buk7456/FreeTX/doc/images/img1.png

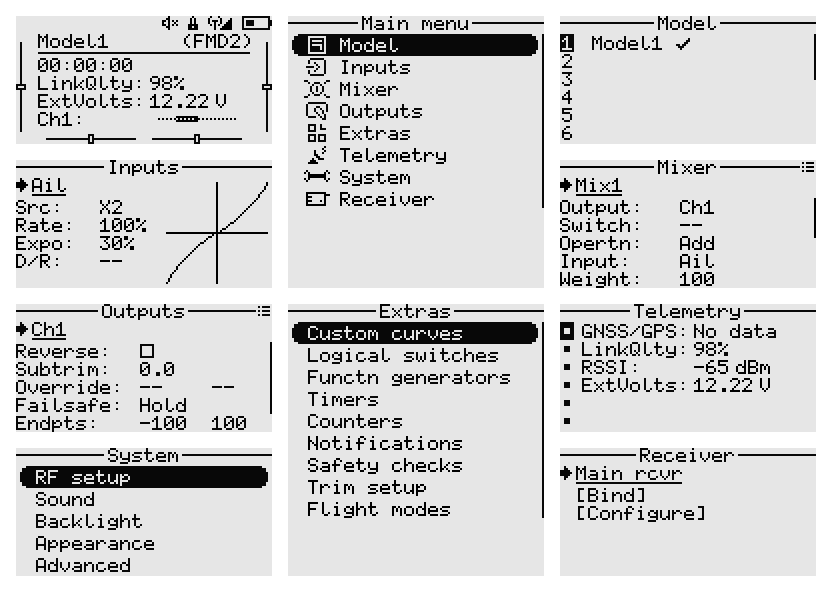
doc/images/img1.png
