buk7456/FreeTX/doc/images/img3.jpg

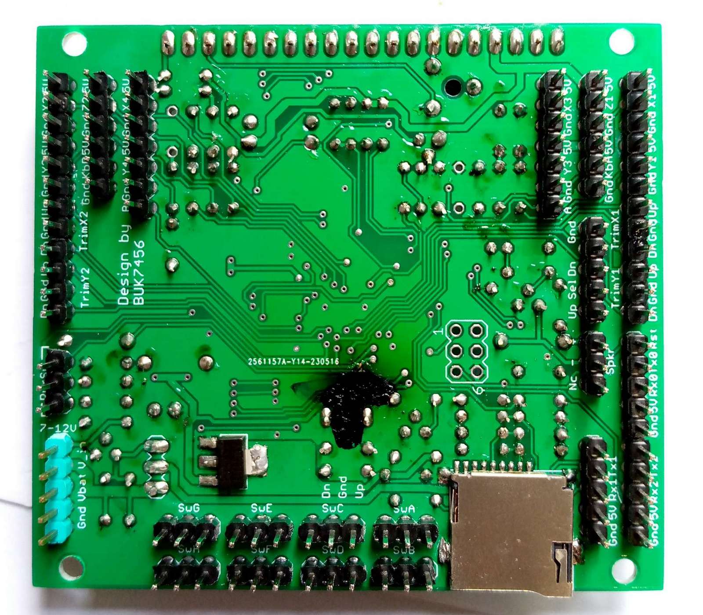
doc/images/img3.jpg
