buk7456/FreeTX/doc/images/img7.jpg

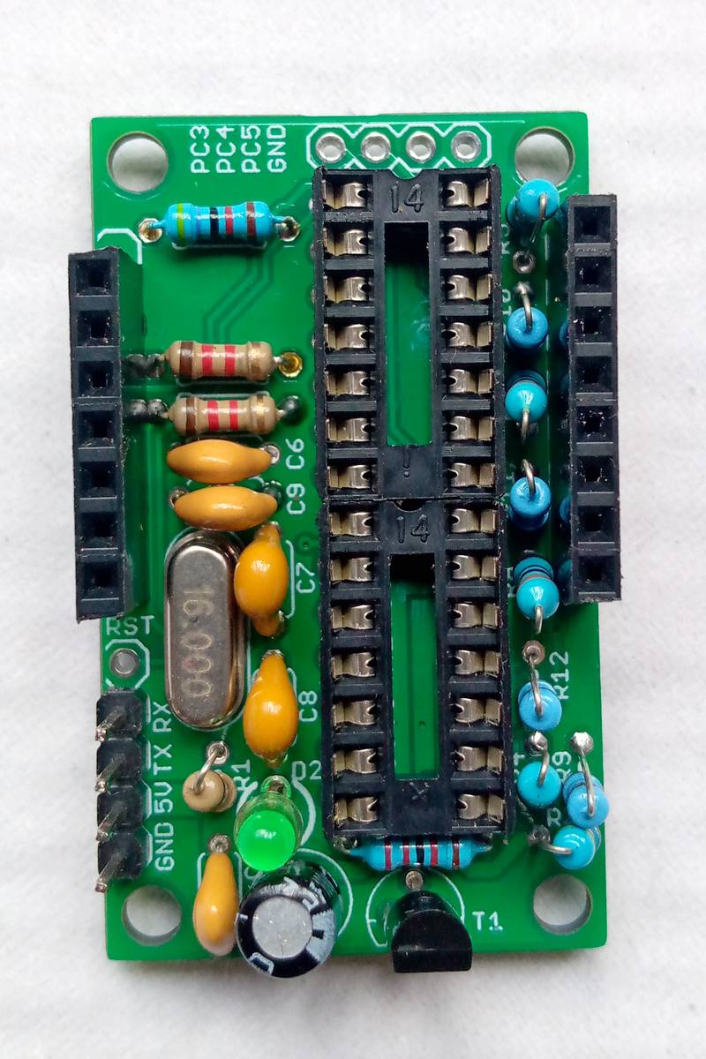
doc/images/img7.jpg
