buk7456/FreeTX/doc/images/img8.jpg

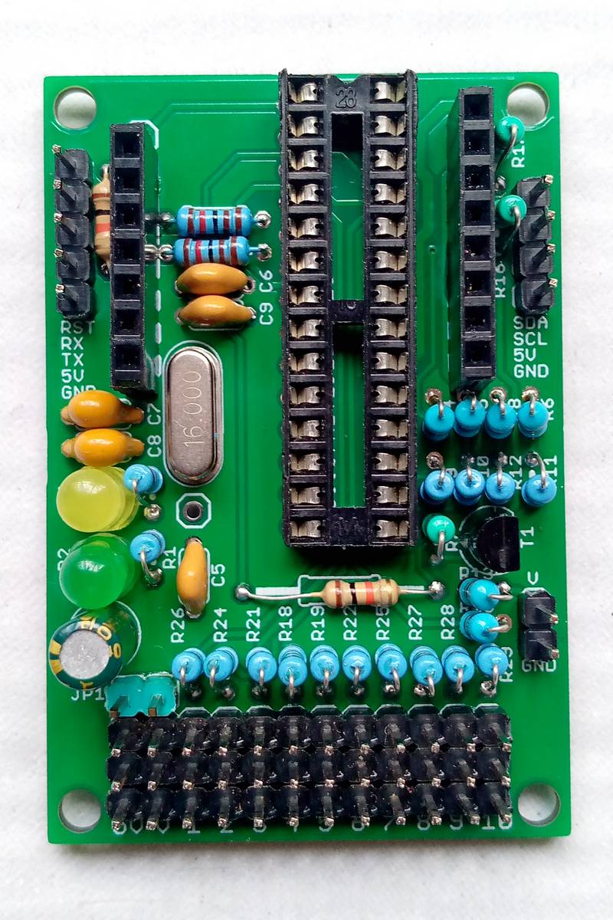
doc/images/img8.jpg
