buk7456/FreeTX/doc/images/img9.jpg

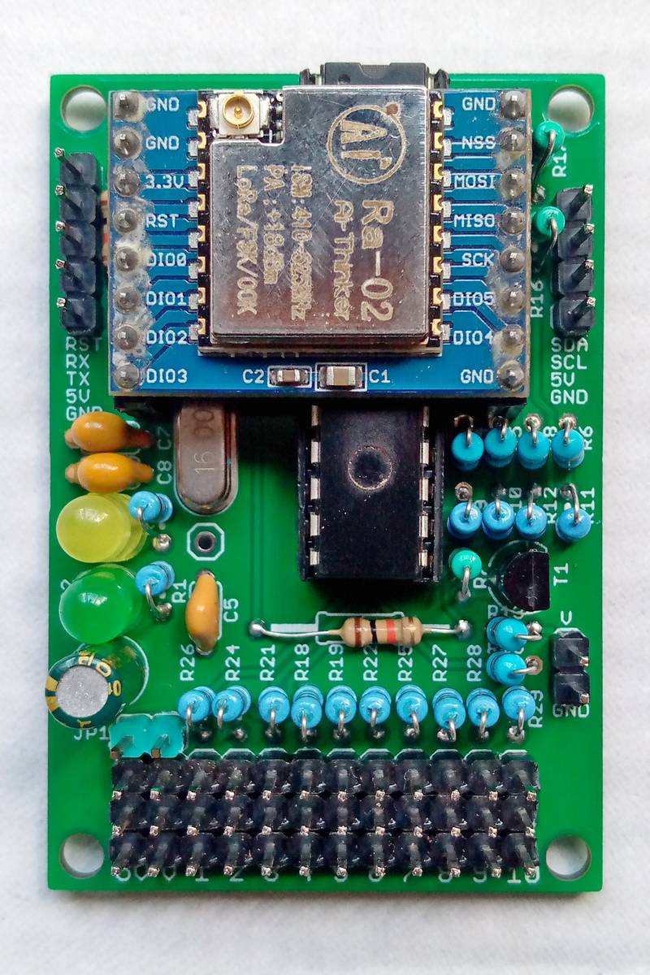
doc/images/img9.jpg
