buk7456/FreeTX/doc/images/screenshots/counters_context_menu.png

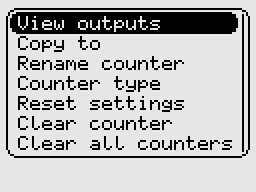
doc/images/screenshots/counters_context_menu.png
