buk7456/FreeTX/doc/images/screenshots/curve_landing_gear_sequencer_1.png

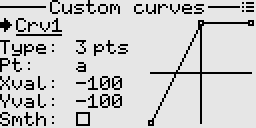
doc/images/screenshots/curve_landing_gear_sequencer_1.png
