buk7456/FreeTX/doc/images/screenshots/curves_landing_gear_sequencer_advanced_v1_1.png

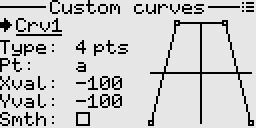
doc/images/screenshots/curves_landing_gear_sequencer_advanced_v1_1.png
