buk7456/FreeTX/doc/images/screenshots/curves_landing_gear_sequencer_advanced_v2_2.png

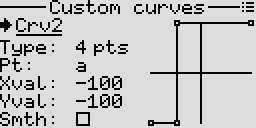
doc/images/screenshots/curves_landing_gear_sequencer_advanced_v2_2.png
