buk7456/FreeTX/doc/images/screenshots/custom_curves_context_menu.png

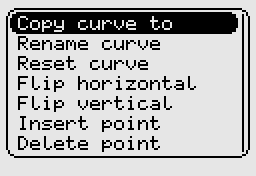
doc/images/screenshots/custom_curves_context_menu.png
