buk7456/FreeTX/doc/images/screenshots/function_generators_context_menu.png

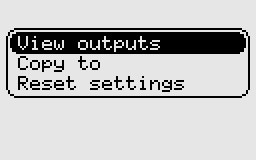
doc/images/screenshots/function_generators_context_menu.png
