buk7456/FreeTX/doc/images/screenshots/home_screen_context_menu.png

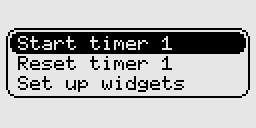
doc/images/screenshots/home_screen_context_menu.png
