buk7456/FreeTX/doc/images/screenshots/inputs_1.png

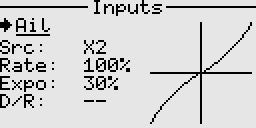
doc/images/screenshots/inputs_1.png
