buk7456/FreeTX/doc/images/screenshots/inputs_2.png

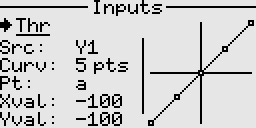
doc/images/screenshots/inputs_2.png
