buk7456/FreeTX/doc/images/screenshots/inputs_3.png

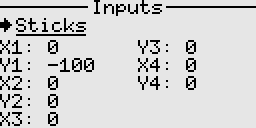
doc/images/screenshots/inputs_3.png
