buk7456/FreeTX/doc/images/screenshots/inputs_4.png

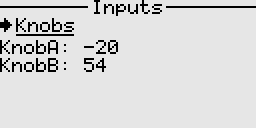
doc/images/screenshots/inputs_4.png
