buk7456/FreeTX/doc/images/screenshots/inputs_5.png

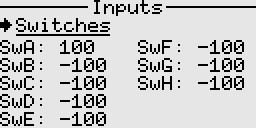
doc/images/screenshots/inputs_5.png
