buk7456/FreeTX/doc/images/screenshots/logical_switches_context_menu.png

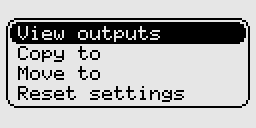
doc/images/screenshots/logical_switches_context_menu.png
