buk7456/FreeTX/doc/images/screenshots/mixer_monitor.png

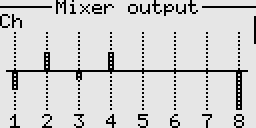
doc/images/screenshots/mixer_monitor.png
