buk7456/FreeTX/doc/images/screenshots/mixer_monitor_with_tooltip.png

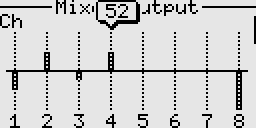
doc/images/screenshots/mixer_monitor_with_tooltip.png
