buk7456/FreeTX/doc/images/screenshots/model_manager_context_menu_free.png

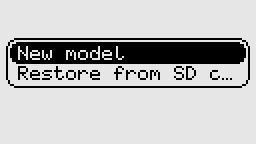
doc/images/screenshots/model_manager_context_menu_free.png
