buk7456/FreeTX/doc/images/screenshots/model_manager_model_type.png

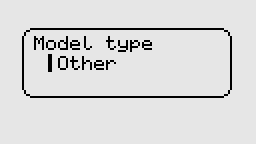
doc/images/screenshots/model_manager_model_type.png
