buk7456/FreeTX/doc/images/screenshots/notifications_context_menu.png

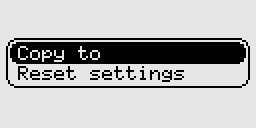
doc/images/screenshots/notifications_context_menu.png
