buk7456/FreeTX/doc/images/screenshots/outputs_context_menu.png

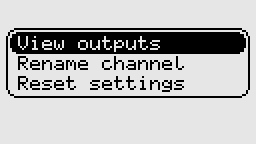
doc/images/screenshots/outputs_context_menu.png
