buk7456/FreeTX/doc/images/screenshots/telemetry_context_menu.png

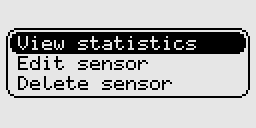
doc/images/screenshots/telemetry_context_menu.png
