buk7456/FreeTX/doc/images/screenshots/telemetry_gnss_context_menu.png

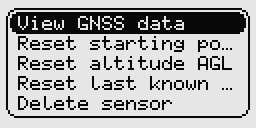
doc/images/screenshots/telemetry_gnss_context_menu.png
