buk7456/FreeTX/doc/images/screenshots/widgets.png

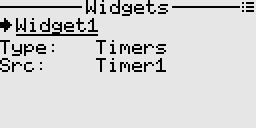
doc/images/screenshots/widgets.png
