buk7456/FreeTX/doc/images/screenshots/widgets_context_menu.png

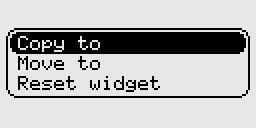
doc/images/screenshots/widgets_context_menu.png
