buk7456/FreeTX/drawings/render_2.jpg

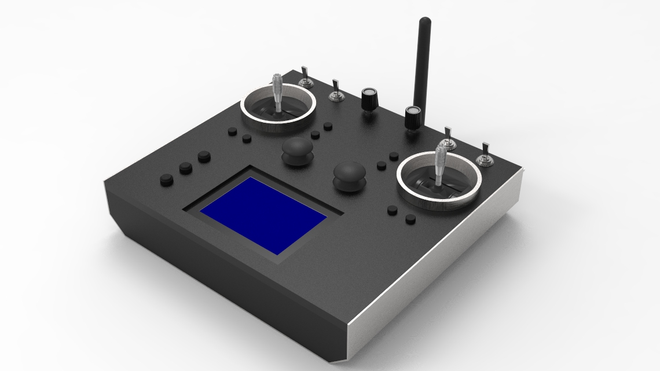
drawings/render_2.jpg
