buk7456/FreeTX/drawings/render_3.jpg

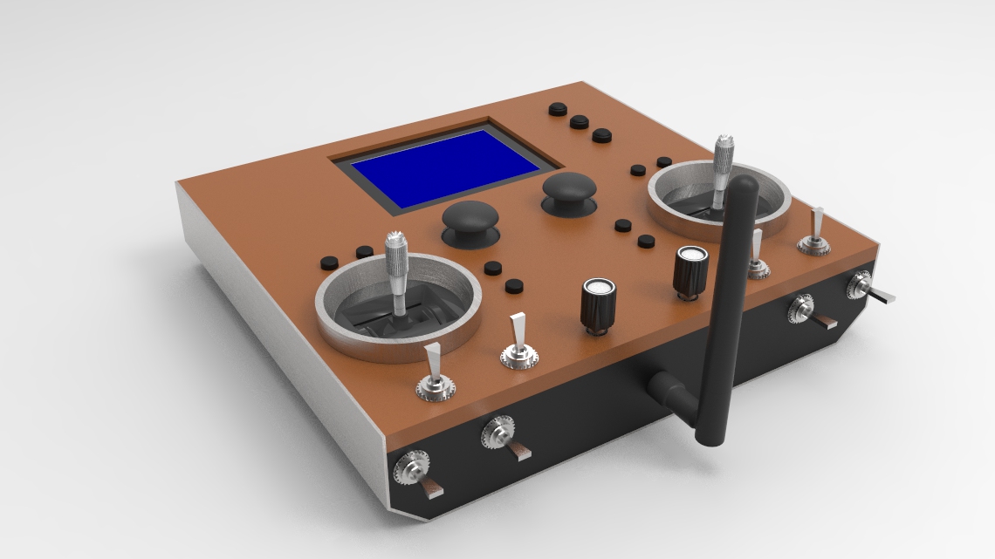
drawings/render_3.jpg
