buk7456/FreeTX/drawings/render_4.jpg

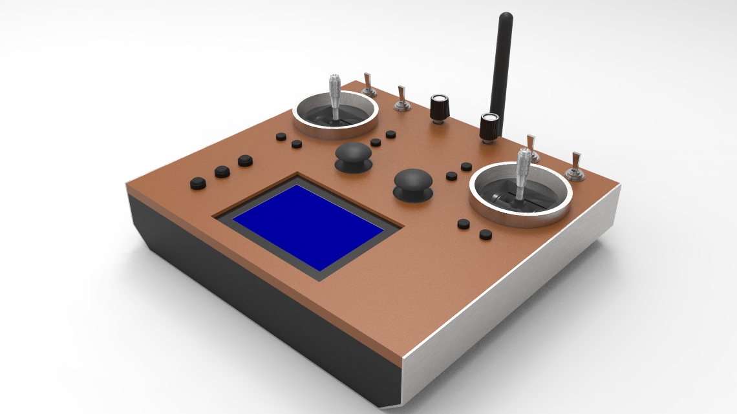
drawings/render_4.jpg
