buk7456/FreeTX/schematics/breakout boards/NRF24L01/board_NRF24L01_v2_bottom.png

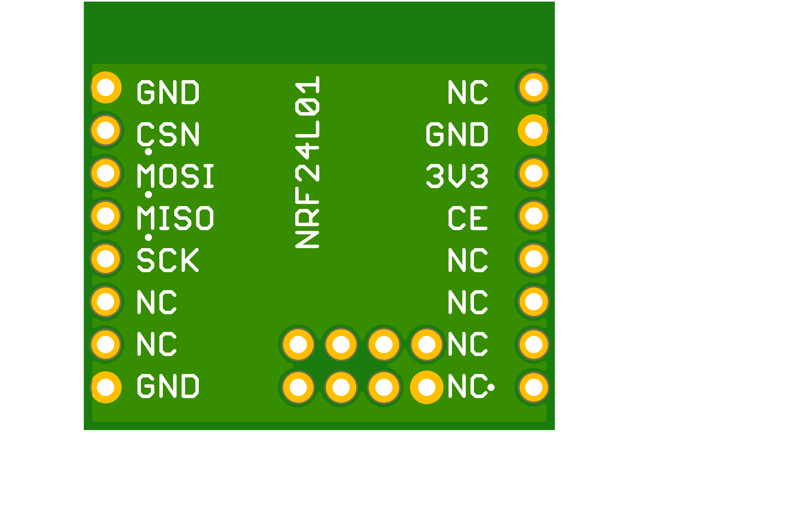
schematics/breakout boards/NRF24L01/board_NRF24L01_v2_bottom.png
