buk7456/FreeTX/schematics/breakout boards/RA-02/board_RA-02_v2_top.png

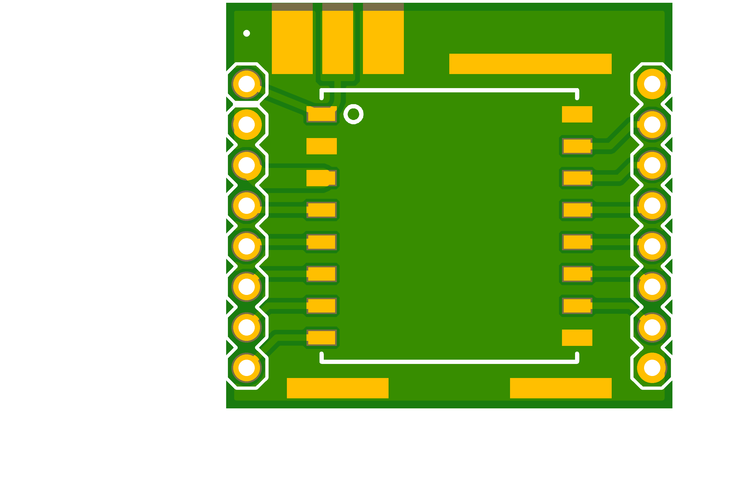
schematics/breakout boards/RA-02/board_RA-02_v2_top.png
