buk7456/FreeTX/schematics/breakout boards/RFM95/board_rfm95_v2_top.png

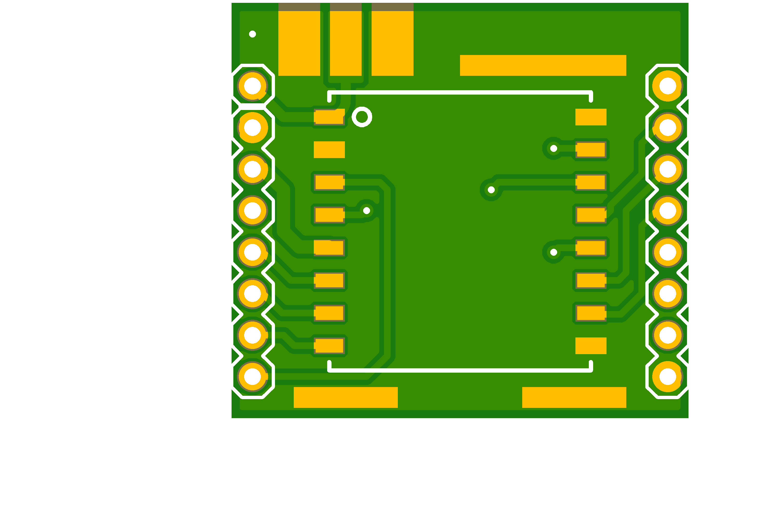
schematics/breakout boards/RFM95/board_rfm95_v2_top.png
