buk7456/FreeTX/schematics/receiver/ra02/receiver_mini_ra02_top.png

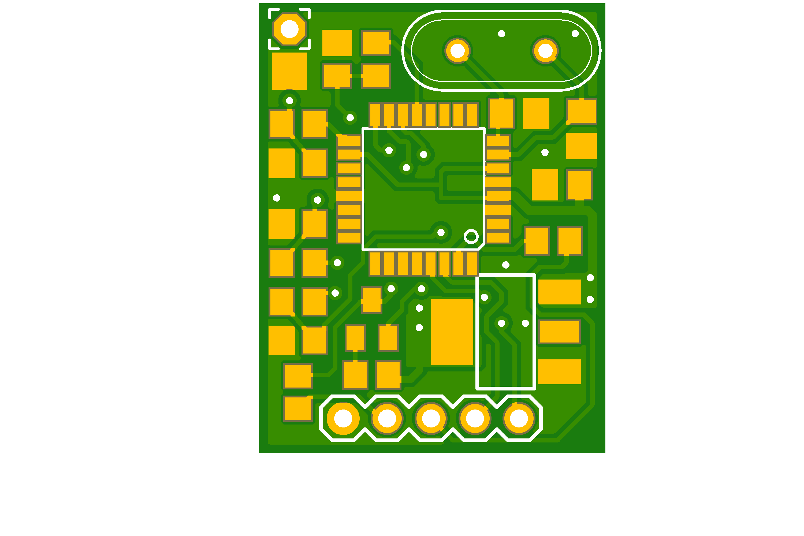
schematics/receiver/ra02/receiver_mini_ra02_top.png
