buk7456/FreeTX/schematics/receiver/ra02/receiver_ra02_bottom.png

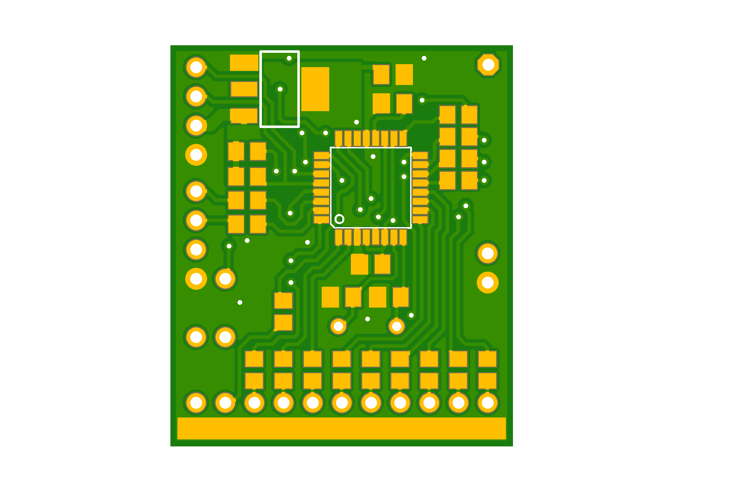
schematics/receiver/ra02/receiver_ra02_bottom.png
