buk7456/FreeTX/schematics/receiver/receiver_v2_bottom.png

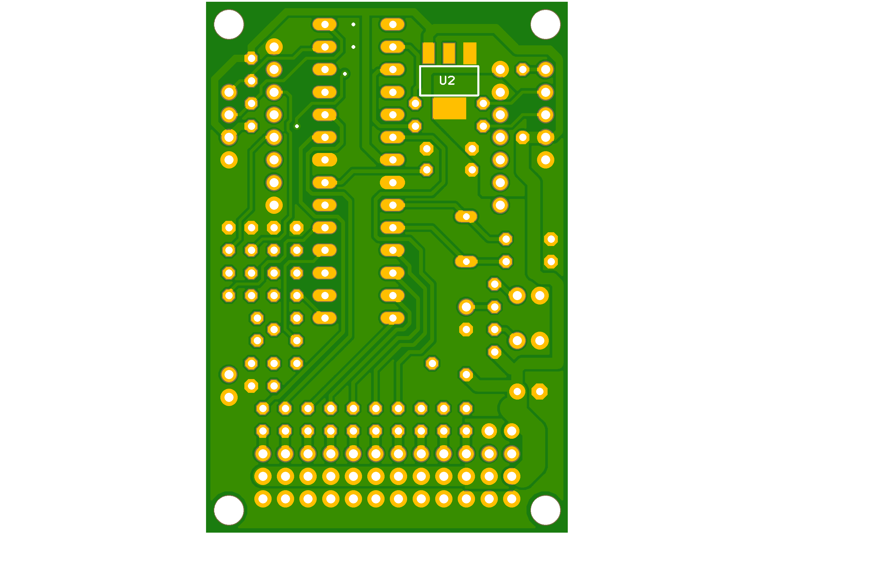
schematics/receiver/receiver_v2_bottom.png
