buk7456/FreeTX/schematics/receiver/receiver_v2_top.png

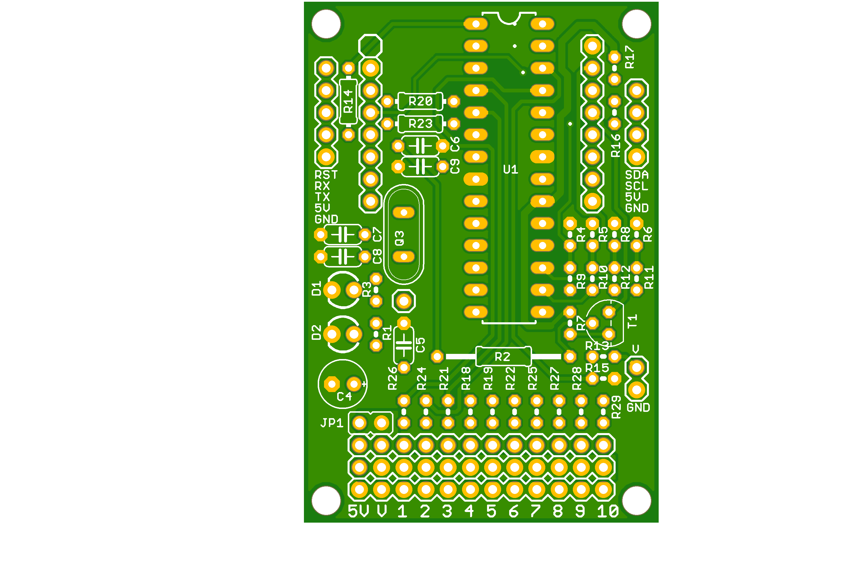
schematics/receiver/receiver_v2_top.png
