buk7456/FreeTX/schematics/receiver/rfm95/receiver_rfm95.bottom.png

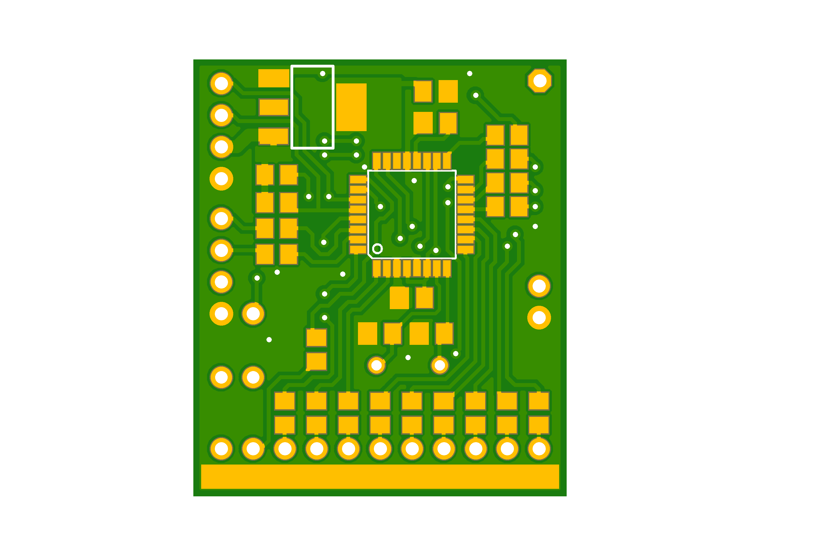
schematics/receiver/rfm95/receiver_rfm95.bottom.png
