buk7456/FreeTX/schematics/transmitter/main/buttons/buttons.bottom.png

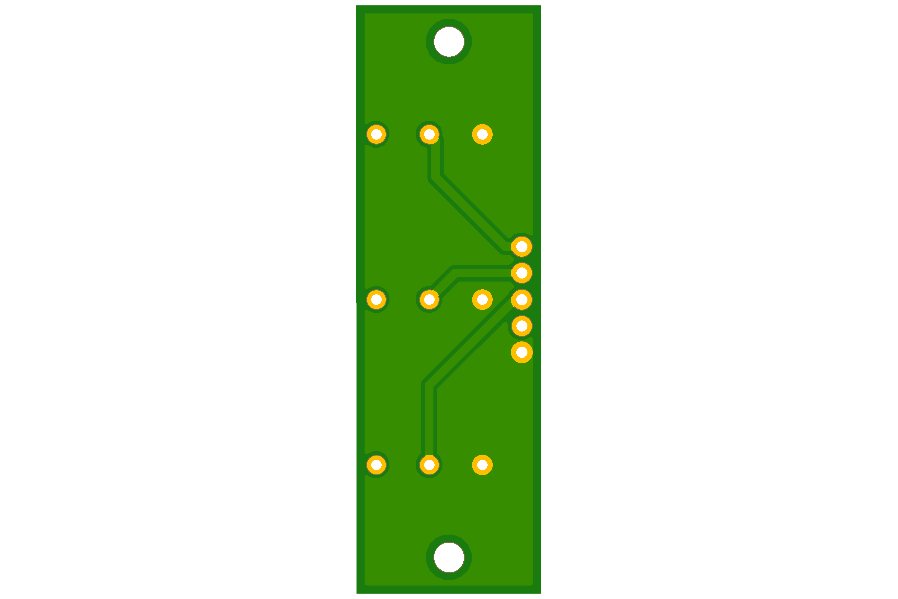
schematics/transmitter/main/buttons/buttons.bottom.png
