buk7456/FreeTX/schematics/transmitter/main/transmitter with KS0108 LCD/transmitter_with_KS0108_LCD_bottom.png

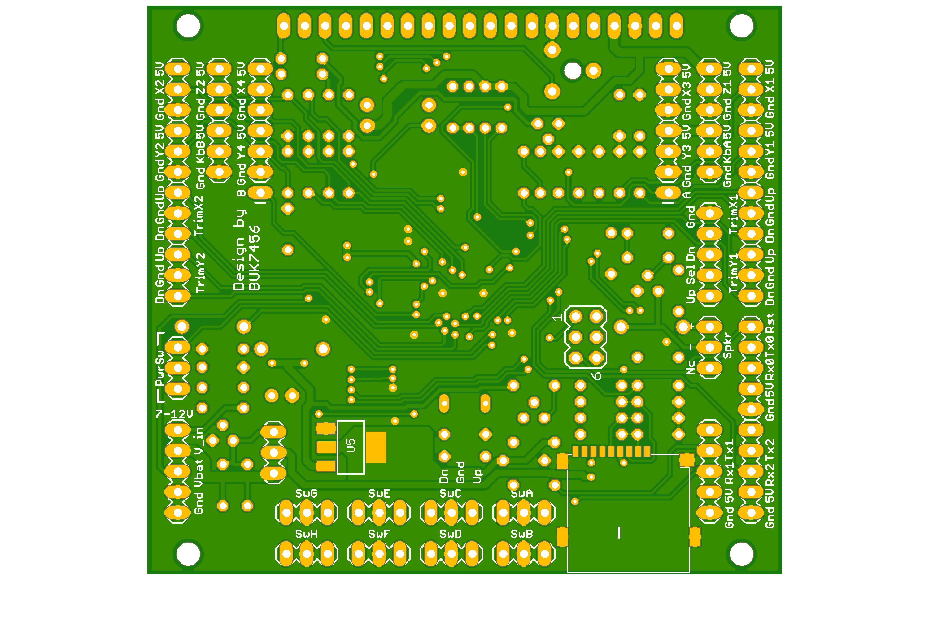
schematics/transmitter/main/transmitter with KS0108 LCD/transmitter_with_KS0108_LCD_bottom.png
