buk7456/FreeTX/schematics/transmitter/main/transmitter with ST7920 LCD/transmitter_with_ST7920_LCD_bottom.png

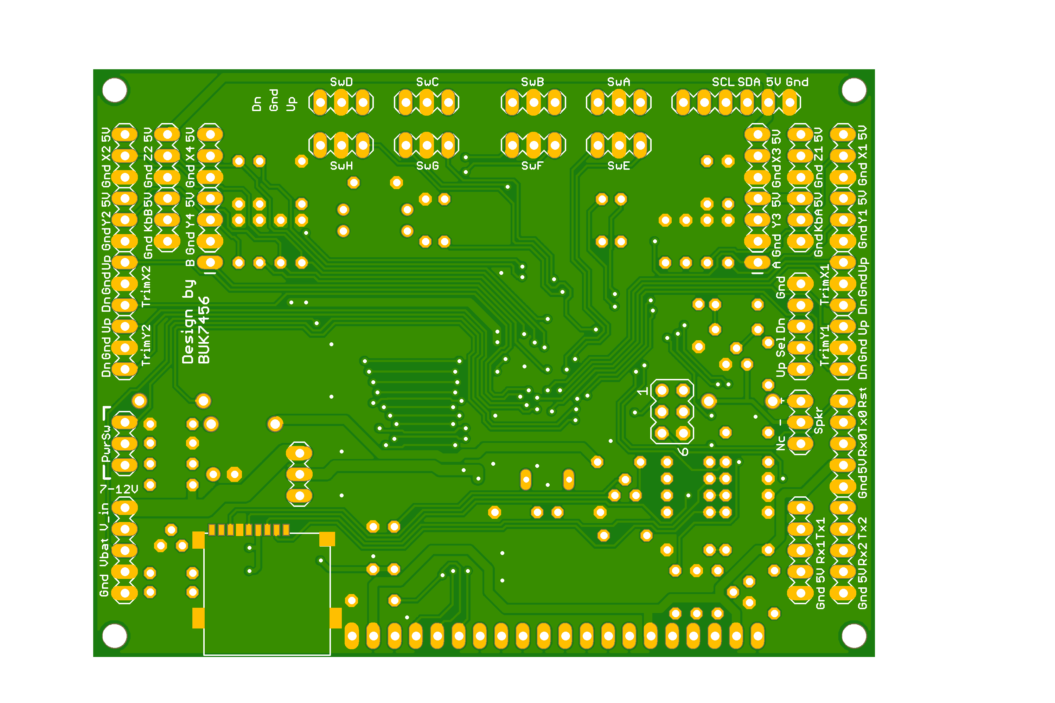
schematics/transmitter/main/transmitter with ST7920 LCD/transmitter_with_ST7920_LCD_bottom.png
