buk7456/FreeTX/schematics/transmitter/main/transmitter with ST7920 LCD/transmitter_with_ST7920_LCD_top.png

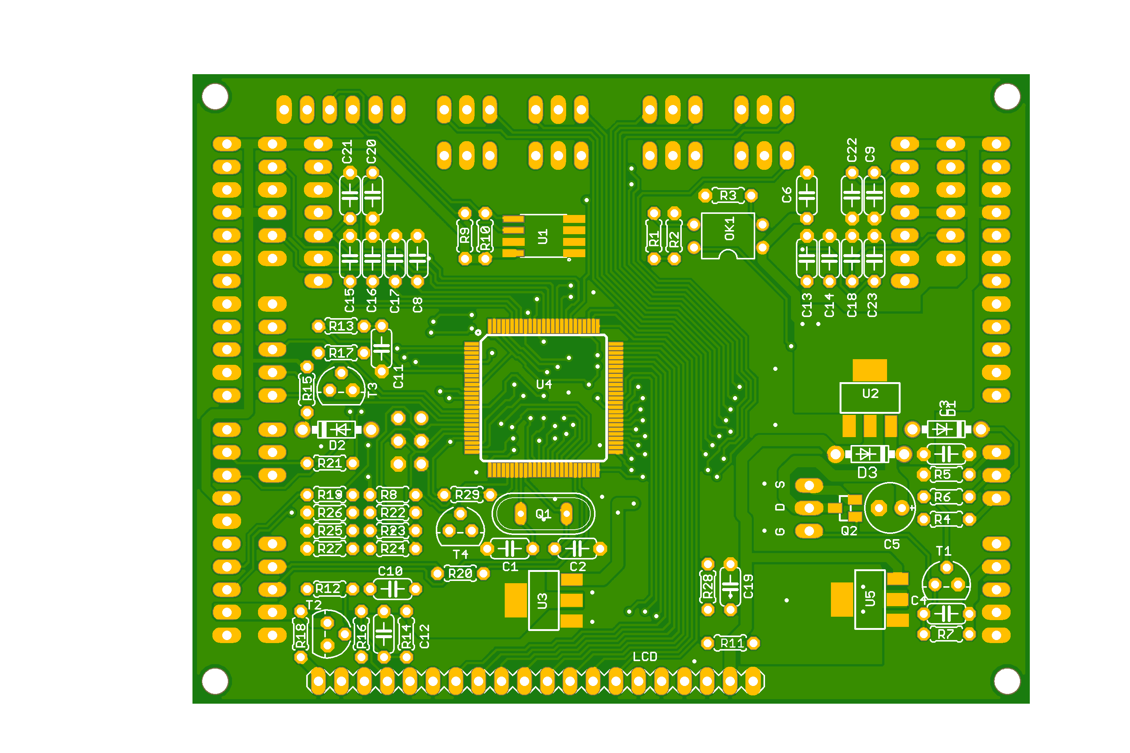
schematics/transmitter/main/transmitter with ST7920 LCD/transmitter_with_ST7920_LCD_top.png
