buk7456/FreeTX/schematics/transmitter/main/trims/trim_switch.bottom.png

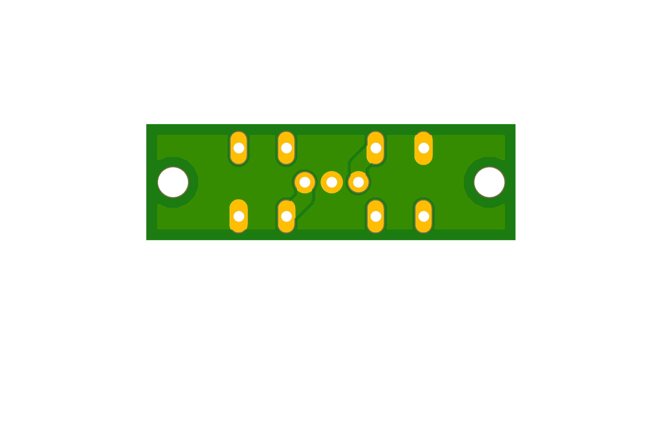
schematics/transmitter/main/trims/trim_switch.bottom.png
