buk7456/FreeTX/schematics/transmitter/secondary/stx_v2_bottom.png

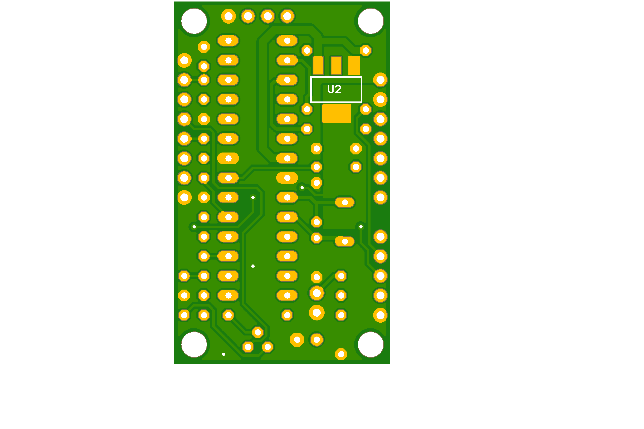
schematics/transmitter/secondary/stx_v2_bottom.png
