buk7456/FreeTX/schematics/transmitter/secondary/stx_v2_top.png

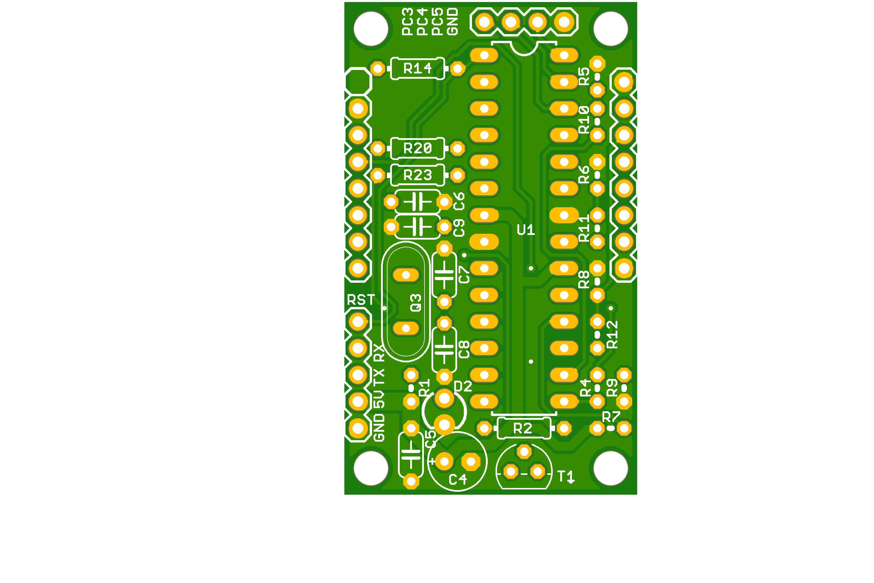
schematics/transmitter/secondary/stx_v2_top.png
