buk7456/FreeTX/drawings/plan_top_plate.pdf

21.00

28.00 | 28.00 | 21.00

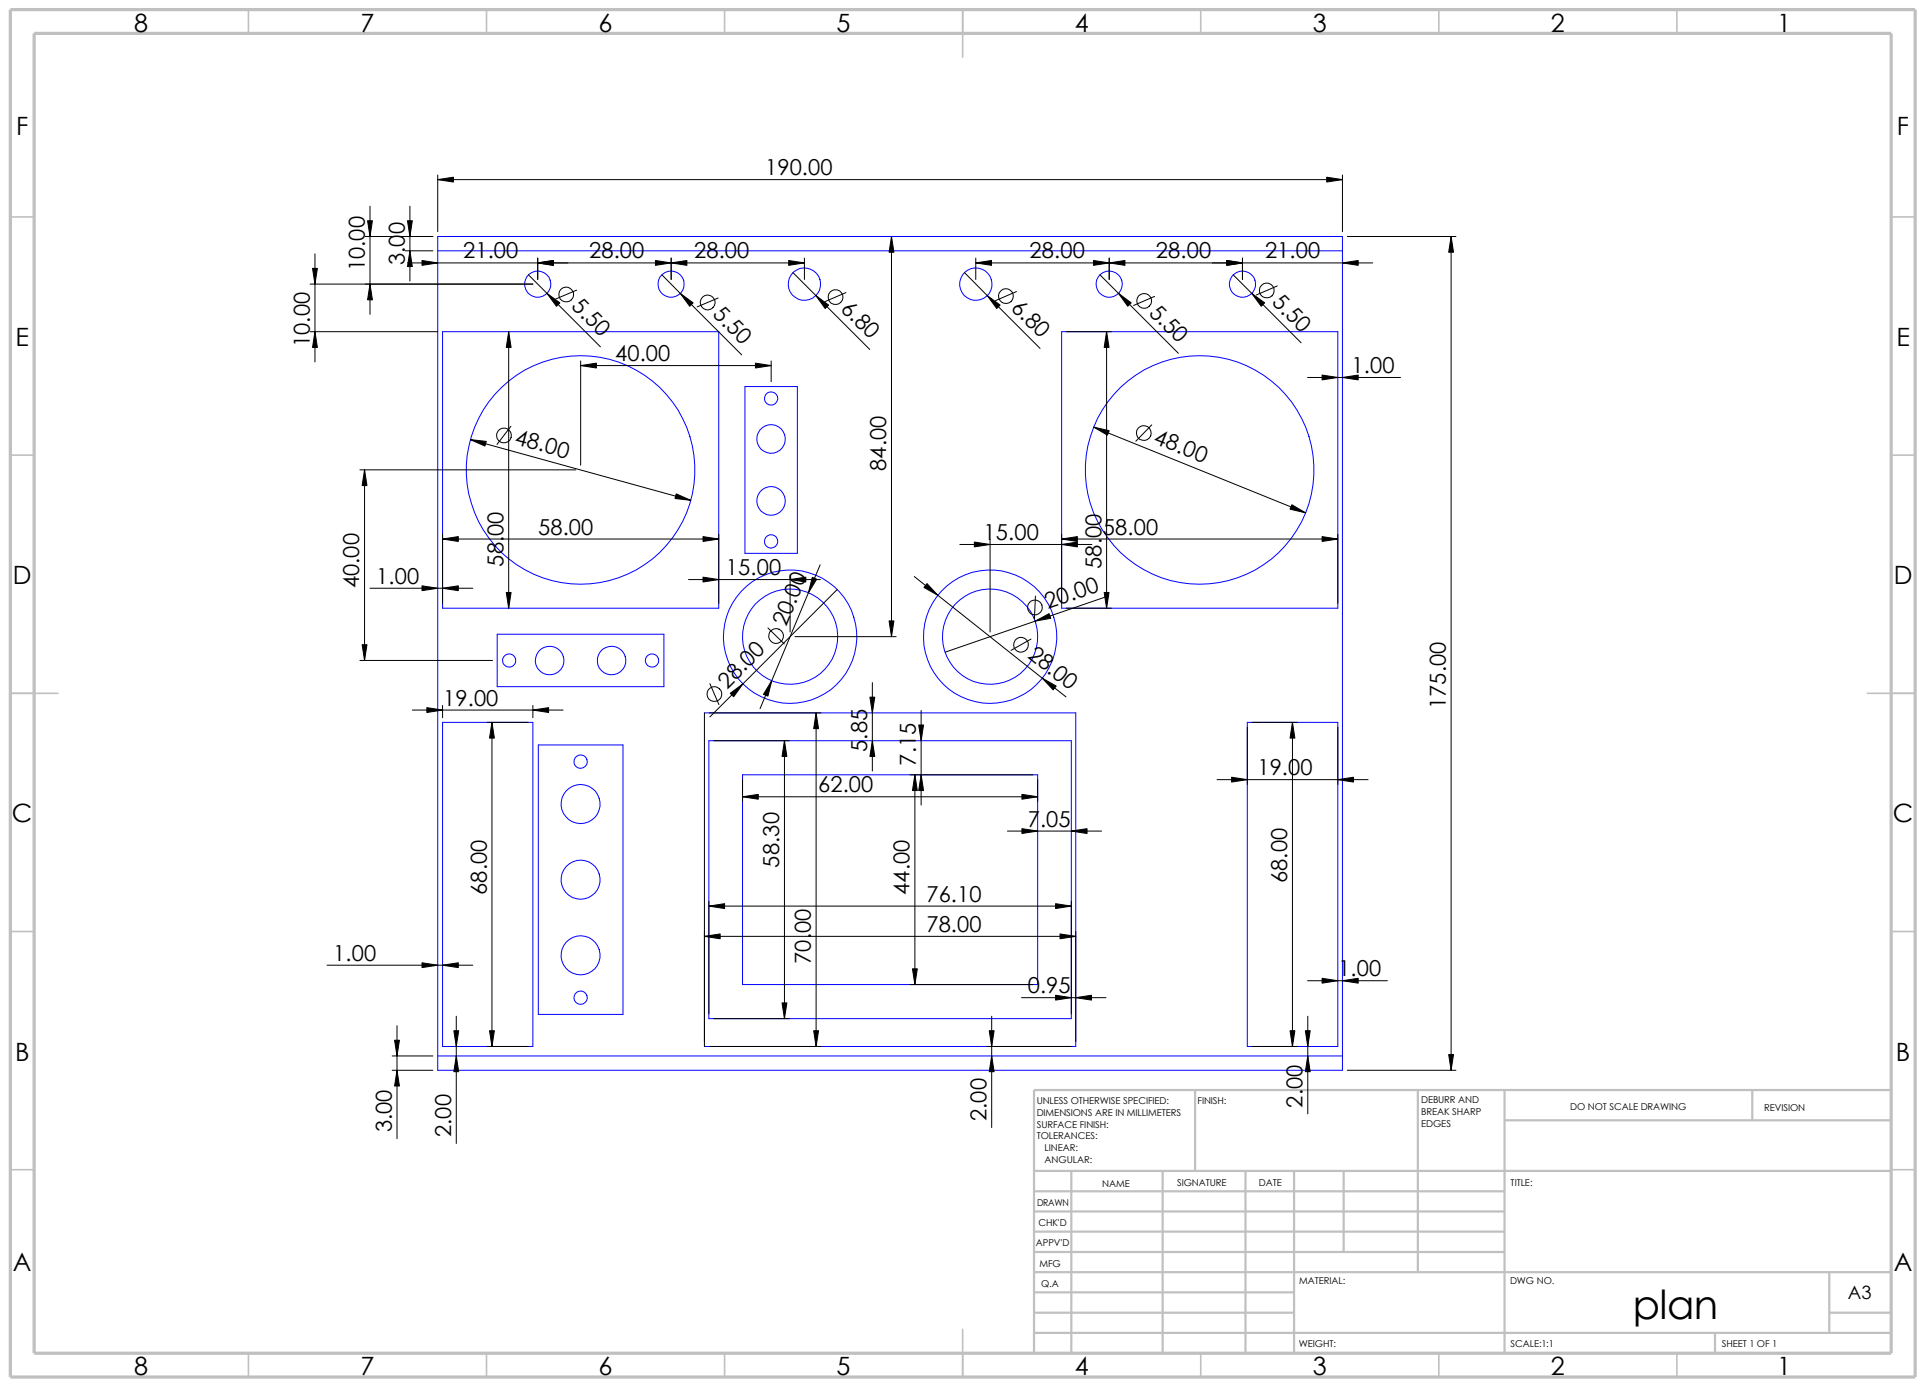
[picture p167: page 1]
SCALE:1:1; SHEET 1 OF 1; WEIGHT:; DO NOT SCALE DRAWING; REVISION; FINISH:; EDGES; DEBURR AND BREAK SHARP

76.10
78.00

UNLESS OTHERWISE SPECIFIED:
DIMENSIONS ARE IN MILLIMETERS
SURFACE FINISH:
TOLERANCES:
LINEAR:
ANGULAR:

NAME | SIGNATURE | DATE | | | | TITLE:

DRAWN

CHK'D

APPV'D

MFG

Q.A | | | | MATERIAL: | DWG NO. plan | A3
