buk7456/FreeTX/drawings/top_plate_a4.pdf

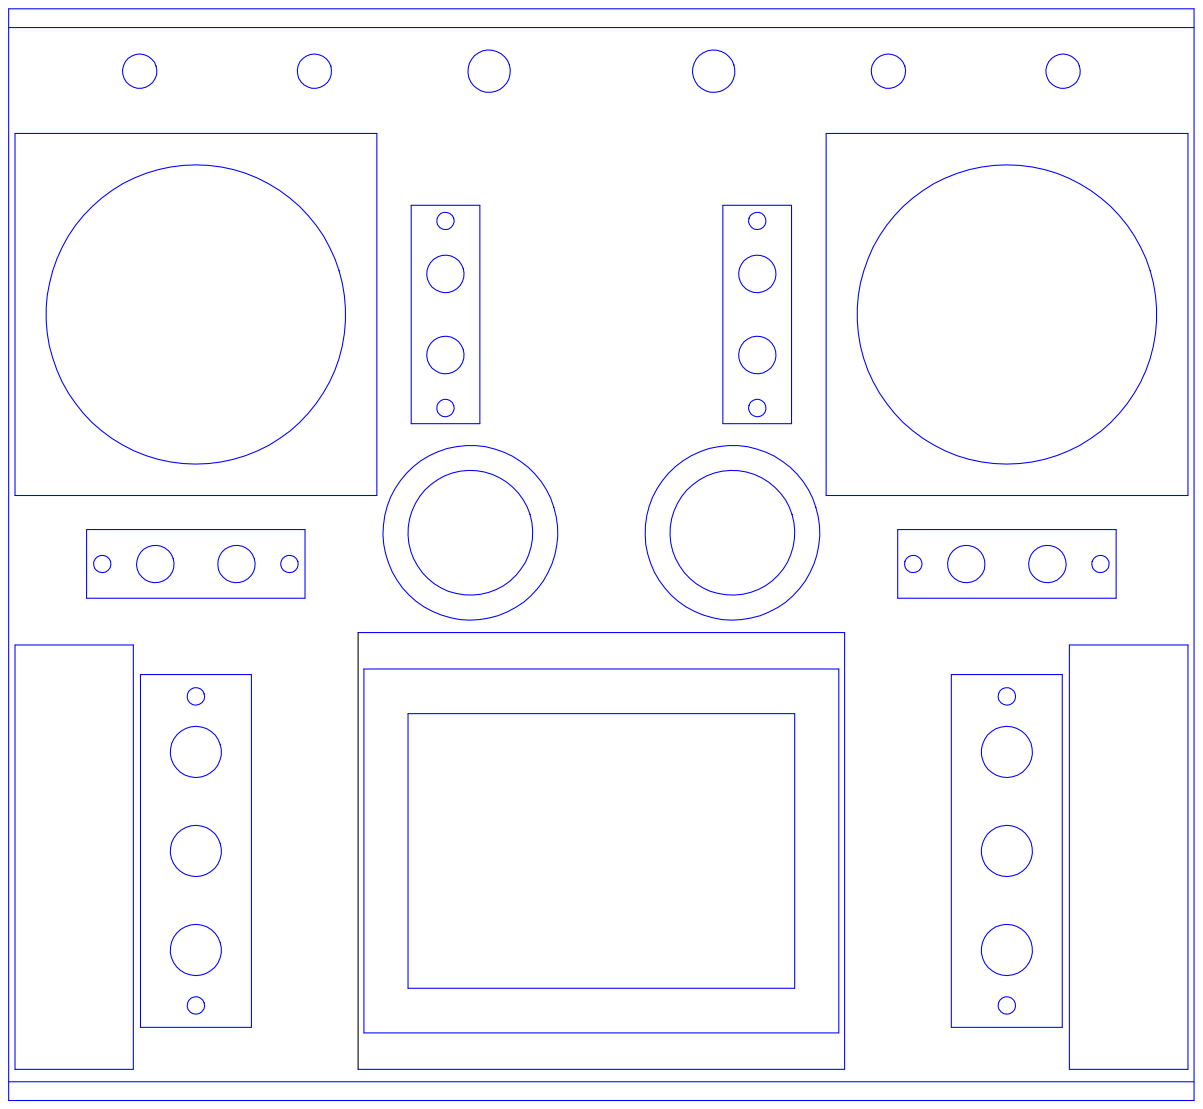
[picture p179: page 1]
