buk7456/FreeTX/schematics/transmitter/main/trims/trim_switch.brd

## EAGLE design schematics/transmitter/main/trims/trim_switch.brd (2023-11-12)

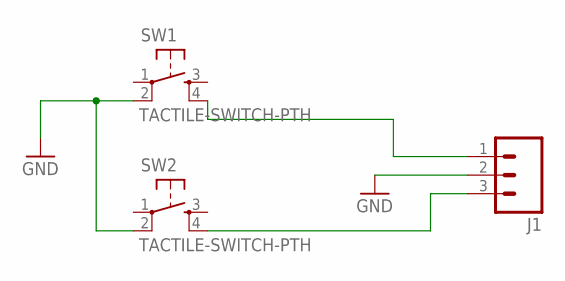
[picture p201: schematic trim_switch.sch]

Parts:
J1: M03PTH; 1X03
SW1, SW2: TACTILE-SWITCH-PTH; TAC-SWITCH-PTH

Connections:
GND: J1.2, SW1.2, SW2.2
unnamed: J1.1, SW1.4
unnamed: J1.3, SW2.4

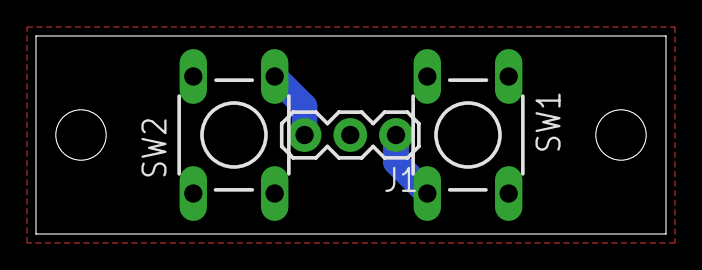
[picture p202: board trim_switch.brd from above]

Board: 2 copper layers, 35.0 x 11.0 mm, 3 parts (0 on the bottom side), 3 nets.
