buk7456/FreeTX/source code/transmitter/mtx/src/mixer.cpp

#include "Arduino.h"

#include "common.h"
#include "mathHelpers.h"
#include "mixer.h"

int32_t applySlow(int32_t currVal, int32_t targetVal, int32_t range, int32_t multiplier, uint32_t riseTime, uint32_t fallTime);
int16_t generateWaveform(uint8_t idx, int32_t _currTime);
void evaluateLogicalSwitches(uint32_t _currTime);
void evaluateCounters();

//mix sources array
int16_t mixSources[MIX_SOURCES_COUNT]; 

//used for graphing inside the mixer screen
int16_t focusedMixInputVal = 0;
int16_t focusedMixOutputVal = 0;
uint8_t focusedMixIdx = 0;

//variables to help with 'delay', 'slow' and 'hold' mixer features
static union {
  int16_t  dlyOldVal[NUM_MIX_SLOTS];
  int16_t  hldOldVal[NUM_MIX_SLOTS];
};
int8_t   dlyPrevOperand[NUM_MIX_SLOTS];  //stored as (operand / 4)
uint8_t  dlyPrevInput[NUM_MIX_SLOTS];
uint32_t dlyStartTime[NUM_MIX_SLOTS];
int32_t  slowCurrVal[NUM_MIX_SLOTS];
uint8_t  hldOldState[NUM_MIX_SLOTS];

//variables to help with logical switches
bool     lsDlyStarted[NUM_LOGICAL_SWITCHES];
uint32_t lsDlyStartTime[NUM_LOGICAL_SWITCHES];
bool     lsDurOldState[NUM_LOGICAL_SWITCHES];
uint32_t lsDurEndTime[NUM_LOGICAL_SWITCHES];
bool     lsToggleLastState[NUM_LOGICAL_SWITCHES];
int32_t  lsDeltaPrevVal[NUM_LOGICAL_SWITCHES];
uint8_t  lsDeltaPrevInput[NUM_LOGICAL_SWITCHES];

//array to store logical switches
bool logicalSwitchState[NUM_LOGICAL_SWITCHES];

bool isReinitialiseMixer = true;

//==================================================================================================

void reinitialiseMixerCalculations()
{
  isReinitialiseMixer = true;
}

//==================================================================================================

void computeChannelOutputs()
{
  if(isCalibratingControls)
    return;

  if(isReinitialiseMixer)
  {
    //reset logical switch states here to avoid stale data in subsequent calculations 
    for(uint8_t i = 0; i < NUM_LOGICAL_SWITCHES; i++)
      logicalSwitchState[i] = false;
    //resynchronize the waveform generators
    for(uint8_t i = 0; i < NUM_FUNCGEN; i++)
      syncWaveform(i);
    // mixSources array
    for(uint8_t i = 0; i < MIX_SOURCES_COUNT; i++)
      mixSources[i] = 0;
  }
  
  //--- Record the current time
  //This ensures consistency of the timing for various stuff irrespective of 
  //the time taken to do all the computations.
  static uint32_t timeOffset;
  if(isReinitialiseMixer)
    timeOffset = millis();
  uint32_t currMillis = millis() - timeOffset;

  //--- Determine the activeFmdIdx 
  //The first one found true takes precedence; the subsequent ones are ignored even if their conditions are met
  activeFmdIdx = 0;
  for(uint8_t i = 0; i < NUM_FLIGHT_MODES; i++)
  {
    if(Model.FlightMode[i].swtch != CTRL_SW_NONE && checkSwitchCondition(Model.FlightMode[i].swtch))
    {
      activeFmdIdx = i;
      break;
    }
  }
  
  flight_mode_t* fmd = &Model.FlightMode[activeFmdIdx];
  
  //--- Get trim values
  //x1 axis
  if(Model.X1Trim.trimState == TRIM_COMMON)
    Model.X1Trim.commonTrim = adjustTrim(0, Model.X1Trim.commonTrim, KEY_X1_TRIM_UP, KEY_X1_TRIM_DOWN);
  else if(Model.X1Trim.trimState == TRIM_FLIGHT_MODE)
    fmd->x1Trim = adjustTrim(0, fmd->x1Trim, KEY_X1_TRIM_UP, KEY_X1_TRIM_DOWN);
  //y1 axis
  if(Model.Y1Trim.trimState == TRIM_COMMON)
    Model.Y1Trim.commonTrim = adjustTrim(1, Model.Y1Trim.commonTrim, KEY_Y1_TRIM_UP, KEY_Y1_TRIM_DOWN);
  else if(Model.Y1Trim.trimState == TRIM_FLIGHT_MODE)
    fmd->y1Trim = adjustTrim(1, fmd->y1Trim, KEY_Y1_TRIM_UP, KEY_Y1_TRIM_DOWN);
  //x2 axis
  if(Model.X2Trim.trimState == TRIM_COMMON)
    Model.X2Trim.commonTrim = adjustTrim(2, Model.X2Trim.commonTrim, KEY_X2_TRIM_UP, KEY_X2_TRIM_DOWN);
  else if(Model.X2Trim.trimState == TRIM_FLIGHT_MODE)
    fmd->x2Trim = adjustTrim(2, fmd->x2Trim, KEY_X2_TRIM_UP, KEY_X2_TRIM_DOWN);
  //y2 axis
  if(Model.Y2Trim.trimState == TRIM_COMMON)
    Model.Y2Trim.commonTrim = adjustTrim(3, Model.Y2Trim.commonTrim, KEY_Y2_TRIM_UP, KEY_Y2_TRIM_DOWN);
  else if(Model.Y2Trim.trimState == TRIM_FLIGHT_MODE)
    fmd->y2Trim = adjustTrim(3, fmd->y2Trim, KEY_Y2_TRIM_UP, KEY_Y2_TRIM_DOWN);
  
  //--- Flight mode trims fade-in
  //Note that the transition time is the time it takes to move from TRIM_MIN_VAL to TRIM_MAX_VAL or vice versa.
  //We also use a multiplier here to improve precision.

  static int32_t  fmdTrimValScaled[4];
  static int32_t  slowFmdTrimValScaled[4];
  static uint32_t flightModeEntryTime;
  static uint8_t  lastFmdIdx;
  const int32_t   scalingFactor = 4096;
  
  fmdTrimValScaled[0] = (int32_t) fmd->x1Trim * scalingFactor;
  fmdTrimValScaled[1] = (int32_t) fmd->y1Trim * scalingFactor;
  fmdTrimValScaled[2] = (int32_t) fmd->x2Trim * scalingFactor;
  fmdTrimValScaled[3] = (int32_t) fmd->y2Trim * scalingFactor;

  if(isReinitialiseMixer)
  {
    lastFmdIdx = activeFmdIdx;
    slowFmdTrimValScaled[0] = fmdTrimValScaled[0];
    slowFmdTrimValScaled[1] = fmdTrimValScaled[1];
    slowFmdTrimValScaled[2] = fmdTrimValScaled[2];
    slowFmdTrimValScaled[3] = fmdTrimValScaled[3];
  }

  if(activeFmdIdx != lastFmdIdx)
  {  
    flightModeEntryTime = currMillis;
    lastFmdIdx = activeFmdIdx;
  }
  
  int16_t  fmdTrimVal[4]; //used inside the mixer loop
  uint32_t tt = fmd->transitionTime * 100;
  for(uint8_t i = 0; i < 4; i++)
  {
    if(currMillis - flightModeEntryTime < tt)
      fmdTrimValScaled[i] = applySlow(slowFmdTrimValScaled[i], fmdTrimValScaled[i], 2 * TRIM_MAX_VAL, scalingFactor, tt, tt);
    slowFmdTrimValScaled[i] = fmdTrimValScaled[i];
    fmdTrimVal[i] = fmdTrimValScaled[i] / scalingFactor;
  }

  ///----------- MIX SOURCES ARRAY INITIALIZATIONS --------

  //Mix source Raw sticks
  for(uint8_t i = 0; i < NUM_STICK_AXES; i++)
    mixSources[SRC_STICK_AXIS_FIRST + i] = stickAxisIn[i];
  
  //Mix source Stick trims

  if(Model.X1Trim.trimState == TRIM_FLIGHT_MODE)
    mixSources[SRC_X1_TRIM] = ((int32_t) fmdTrimVal[0] * 5) / 10 ;
  else if(Model.X1Trim.trimState == TRIM_COMMON)
    mixSources[SRC_X1_TRIM] = ((int32_t) Model.X1Trim.commonTrim * 5) / 10;
  else if(Model.X1Trim.trimState == TRIM_DISABLED)
    mixSources[SRC_X1_TRIM] = 0;
  
  if(Model.Y1Trim.trimState == TRIM_FLIGHT_MODE)
    mixSources[SRC_Y1_TRIM] = ((int32_t) fmdTrimVal[1] * 5) / 10 ;
  else if(Model.Y1Trim.trimState == TRIM_COMMON)
    mixSources[SRC_Y1_TRIM] = ((int32_t) Model.Y1Trim.commonTrim * 5) / 10;
  else if(Model.Y1Trim.trimState == TRIM_DISABLED)
    mixSources[SRC_Y1_TRIM] = 0;

  if(Model.X2Trim.trimState == TRIM_FLIGHT_MODE)
    mixSources[SRC_X2_TRIM] = ((int32_t) fmdTrimVal[2] * 5) / 10 ;
  else if(Model.X2Trim.trimState == TRIM_COMMON)
    mixSources[SRC_X2_TRIM] = ((int32_t) Model.X2Trim.commonTrim * 5) / 10;
  else if(Model.X2Trim.trimState == TRIM_DISABLED)
    mixSources[SRC_X2_TRIM] = 0;

  if(Model.Y2Trim.trimState == TRIM_FLIGHT_MODE)
    mixSources[SRC_Y2_TRIM] = ((int32_t) fmdTrimVal[3] * 5) / 10 ;
  else if(Model.Y2Trim.trimState == TRIM_COMMON)
    mixSources[SRC_Y2_TRIM] = ((int32_t) Model.Y2Trim.commonTrim * 5) / 10;
  else if(Model.Y2Trim.trimState == TRIM_DISABLED)
    mixSources[SRC_Y2_TRIM] = 0;

  //Mix source Knobs
  for(uint8_t i = 0; i < NUM_KNOBS; i++)
    mixSources[SRC_KNOB_FIRST + i] = knobIn[i];
  
  //Mix source 100 Percent i.e. Max
  mixSources[SRC_100PERC] = 500;
  
  //Mix source Rud, Ail, Ele
  //Handle dual rate and expo
  //Rud
  if(Model.RudDualRate.swtch == CTRL_SW_NONE || !checkSwitchCondition(Model.RudDualRate.swtch))
    mixSources[SRC_RUD] = calcRateExpo(mixSources[Model.rudSrcRaw], Model.RudDualRate.rate1, Model.RudDualRate.expo1);
  else 
    mixSources[SRC_RUD] = calcRateExpo(mixSources[Model.rudSrcRaw], Model.RudDualRate.rate2, Model.RudDualRate.expo2);
  //Ail
  if(Model.AilDualRate.swtch == CTRL_SW_NONE || !checkSwitchCondition(Model.AilDualRate.swtch))
    mixSources[SRC_AIL] = calcRateExpo(mixSources[Model.ailSrcRaw], Model.AilDualRate.rate1, Model.AilDualRate.expo1);
  else 
    mixSources[SRC_AIL] = calcRateExpo(mixSources[Model.ailSrcRaw], Model.AilDualRate.rate2, Model.AilDualRate.expo2);
  //Ele
  if(Model.EleDualRate.swtch == CTRL_SW_NONE || !checkSwitchCondition(Model.EleDualRate.swtch))
    mixSources[SRC_ELE] = calcRateExpo(mixSources[Model.eleSrcRaw], Model.EleDualRate.rate1, Model.EleDualRate.expo1);
  else 
    mixSources[SRC_ELE] = calcRateExpo(mixSources[Model.eleSrcRaw], Model.EleDualRate.rate2, Model.EleDualRate.expo2);
  
  //Mix source Throttle curve
  int16_t _xxQQ[MAX_NUM_POINTS_CUSTOM_CURVE];
  int16_t _yyQQ[MAX_NUM_POINTS_CUSTOM_CURVE];
  for(uint8_t pt = 0; pt < Model.ThrottleCurve.numPoints; pt++)
  {
    _xxQQ[pt] = 5 * Model.ThrottleCurve.xVal[pt];
    _yyQQ[pt] = 5 * Model.ThrottleCurve.yVal[pt];
  }
  if(Model.ThrottleCurve.smooth)
    mixSources[SRC_THR] = cubicHermiteInterpolate(_xxQQ, _yyQQ, Model.ThrottleCurve.numPoints, mixSources[Model.thrSrcRaw]);
  else
    mixSources[SRC_THR] = linearInterpolate(_xxQQ, _yyQQ, Model.ThrottleCurve.numPoints, mixSources[Model.thrSrcRaw]);

  //Mix source Switches
  for(uint8_t i = 0; i < NUM_PHYSICAL_SWITCHES; i++)
  {
    if(Sys.swType[i] == SW_2POS || Sys.swType[i] == SW_2POS_MOMENTARY)
      mixSources[SRC_SW_PHYSICAL_FIRST + i] = (swState[i] == SWLOWERPOS) ? 500 : -500;
    else if(Sys.swType[i] == SW_3POS || Sys.swType[i] == SW_3POS_MOMENTARY)
      mixSources[SRC_SW_PHYSICAL_FIRST + i] = (swState[i] == SWLOWERPOS) ? 500 : ((swState[i] == SWUPPERPOS) ? -500 : 0);
    else if(Sys.swType[i] == SW_ABSENT)
      mixSources[SRC_SW_PHYSICAL_FIRST + i] = 0;
  }
  
  //Mix sources Function generators
  for(uint8_t i = 0; i < NUM_FUNCGEN; i++)
    mixSources[SRC_FUNCGEN_FIRST + i] = generateWaveform(i, currMillis);

  //Evaluate counters
  evaluateCounters();

  //Mix sources Logical switches
  evaluateLogicalSwitches(currMillis);
  for(uint8_t i = 0; i < NUM_LOGICAL_SWITCHES; i++)
    mixSources[SRC_SW_LOGICAL_FIRST + i] = logicalSwitchState[i] ? 500 : -500;
  
  //Mix sources Channels
  for(uint8_t i = 0; i < NUM_RC_CHANNELS; i++)
    mixSources[SRC_CH1 + i] = 0;
  
  //Mix sources Virtual channels
  for(uint8_t i = 0; i < NUM_VIRTUAL_CHANNELS; i++)
    mixSources[SRC_VIRTUAL_FIRST + i] = 0;

  focusedMixInputVal = 0;
  focusedMixOutputVal = 0;
  
  ///----------------- MIXER LOOP ------------------------
  
  for(uint8_t mixIdx = 0; mixIdx < NUM_MIX_SLOTS; mixIdx++)
  {
    mixer_params_t *mxr = &Model.Mixer[mixIdx];
    
    //--- CHECK OUTPUT INDEX
    if(mxr->output == SRC_NONE)
      continue;
    
    //--- HANDLE SPECIAL MIXER OPERATION 'HOLD'
    if(isReinitialiseMixer)
      hldOldState[mixIdx] = false;
    if(mxr->operation == MIX_HOLD)
    {
      if(checkSwitchCondition(mxr->swtch))
      {
        //capture the value at the instant of activating the control switch
        if(!hldOldState[mixIdx])
        {
          hldOldState[mixIdx] = true;
          hldOldVal[mixIdx] = mixSources[mxr->output];
        }
        //override the source with the value we captured
        mixSources[mxr->output] = hldOldVal[mixIdx];
      }
      else
        hldOldState[mixIdx] = false;

      continue;
    }
    
    //--- CHECK INPUT INDEX
    if(mxr->input == SRC_NONE)
      continue;

    //--- ASSIGN
    int16_t operand = 0;
    if(mxr->input < MIX_SOURCES_COUNT)
      operand = mixSources[mxr->input];
    else if(mxr->input >= SRC_COUNTER_FIRST && mxr->input <= SRC_COUNTER_LAST)
    {
      uint8_t counterIdx = mxr->input - SRC_COUNTER_FIRST;
      operand = -500 + ((int32_t)counterOut[counterIdx] * 1000 / (Model.Counter[counterIdx].modulus - 1));
    }

    //--- DELAY
    //Reset delay variables if the input or model has been changed
    if((mxr->input != dlyPrevInput[mixIdx]) || isReinitialiseMixer) 
    {
      dlyPrevInput[mixIdx] = mxr->input;
      dlyOldVal[mixIdx]  = operand;
      dlyPrevOperand[mixIdx]  = operand / 4;
      dlyStartTime[mixIdx] = currMillis;
    }
    //For the comparisons below, we add some hysteresis to counteract the jitter in analog readings.
    const int16_t hystVal = 4; //empirically determined value
    int8_t difference = (operand / 4) - dlyPrevOperand[mixIdx]; 
    if(abs(difference) > (hystVal / 4))
    {
      dlyStartTime[mixIdx] = currMillis;
      dlyPrevOperand[mixIdx] = operand / 4;
    }
    if(operand > (dlyOldVal[mixIdx] + hystVal))
    {
      if(mxr->delayUp != 0) //only compute when necessary
      {
        if((currMillis - dlyStartTime[mixIdx]) < ((uint32_t)mxr->delayUp * 100))
          operand = dlyOldVal[mixIdx];
        else
          dlyOldVal[mixIdx] = operand;
      }
      else
        dlyOldVal[mixIdx] = operand;
    }
    else if(operand < (dlyOldVal[mixIdx] - hystVal))
    {
      if(mxr->delayDown != 0) //only compute when necessary
      {
        if((currMillis - dlyStartTime[mixIdx]) < ((uint32_t)mxr->delayDown * 100))
          operand = dlyOldVal[mixIdx];
        else
          dlyOldVal[mixIdx] = operand;
      }
      else
        dlyOldVal[mixIdx] = operand;
    }
    
    //--- SLOW
    //We use a multiplier value here to improve precision
    const int32_t _factor = 4096;
    if(isReinitialiseMixer)
      slowCurrVal[mixIdx] = _factor * operand;
    int32_t _op = _factor * operand;
    if(mxr->slowUp != 0 || mxr->slowDown != 0) //only compute when necessary
    {
      _op = applySlow(slowCurrVal[mixIdx], _op, 2 * 500, _factor, (uint32_t)mxr->slowUp * 100, (uint32_t)mxr->slowDown * 100);
      slowCurrVal[mixIdx] = _op;
      operand = _op/_factor;
    }
    else //keep the stored value up to date
      slowCurrVal[mixIdx] = _op;
     
    //--- CHECK MIXSWITCH, FLIGHT MODE
    //This is done after processing Delay and Slow so we can still update them 
    //even when the mixer condition is not met to avoid glitches due to stale values.
    if(!checkSwitchCondition(mxr->swtch) || !((mxr->flightMode >> activeFmdIdx) & 0x01))
      continue;

    if(focusedMixIdx == mixIdx)
      focusedMixInputVal = operand;
    
    //--- CURVES
    if(mxr->curveType == MIX_CURVE_TYPE_EXPO)
      operand = calcExpo(operand, mxr->curveVal);
    else if(mxr->curveType == MIX_CURVE_TYPE_CUSTOM)
    {
      uint8_t _crvIdx = mxr->curveVal;
      uint8_t _numPts = Model.CustomCurve[_crvIdx].numPoints;
      int16_t _xx[MAX_NUM_POINTS_CUSTOM_CURVE];
      int16_t _yy[MAX_NUM_POINTS_CUSTOM_CURVE];
      for(uint8_t pt = 0; pt < _numPts; pt++)
      {
        _xx[pt] = 5 * Model.CustomCurve[_crvIdx].xVal[pt];
        _yy[pt] = 5 * Model.CustomCurve[_crvIdx].yVal[pt];
      }
      if(Model.CustomCurve[_crvIdx].smooth)
        operand = cubicHermiteInterpolate(_xx, _yy, _numPts, operand);
      else
        operand = linearInterpolate(_xx, _yy, _numPts, operand);
    }
    else if(mxr->curveType == MIX_CURVE_TYPE_FUNCTION)
    {
      uint8_t _func = mxr->curveVal;
      switch(_func)
      {
        case MIX_CURVE_FUNC_X_GREATER_THAN_ZERO: 
          if(operand < 0) operand = 0; 
          break;
        case MIX_CURVE_FUNC_X_LESS_THAN_ZERO: 
          if(operand > 0) operand = 0; 
          break;
        case MIX_CURVE_FUNC_ABS_X: 
          if(operand < 0) operand = -operand; 
          break;
      }
    }
    
    //--- WEIGHT, OFFSET
    operand = weightAndOffset(operand, mxr->weight, mxr->offset);
    
    //--- DIFFERENTIAL
    if(mxr->curveType == MIX_CURVE_TYPE_DIFF && mxr->curveVal != 0)
      operand = calcDifferential(operand, mxr->curveVal);

    //Export for graphing purposes
    if(focusedMixIdx == mixIdx)
    {
      focusedMixOutputVal = operand;
      focusedMixOutputVal = constrain(focusedMixOutputVal, -500, 500);
    }
    
    //--- TRIM
    //Apply weighted trim after differential to prevent the output being erratic when differential or
    //curves are specified and trim is non-zero.
    if(mxr->trimEnabled)
    {
      uint8_t src = mxr->input;
      if(src == SRC_RUD) src = Model.rudSrcRaw;
      if(src == SRC_THR) src = Model.thrSrcRaw;
      if(src == SRC_AIL) src = Model.ailSrcRaw;
      if(src == SRC_ELE) src = Model.eleSrcRaw;
      
      if(src == SRC_X1_AXIS) operand += ((int32_t) mixSources[SRC_X1_TRIM] * mxr->weight) / 100; 
      else if(src == SRC_Y1_AXIS) operand += ((int32_t) mixSources[SRC_Y1_TRIM] * mxr->weight) / 100; 
      else if(src == SRC_X2_AXIS) operand += ((int32_t) mixSources[SRC_X2_TRIM] * mxr->weight) / 100; 
      else if(src == SRC_Y2_AXIS) operand += ((int32_t) mixSources[SRC_Y2_TRIM] * mxr->weight) / 100; 
    }
    
    //--- MIX AND UPDATE
    operand = constrain(operand, -500, 500); 
    int32_t output = mixSources[mxr->output];
    switch(mxr->operation)
    {
      case MIX_ADD:
        output += operand;
        break;
        
      case MIX_MULTIPLY:
        output *= operand;
        output /= 500; 
        break;
        
      case MIX_REPLACE:
        output = operand;
        break;
    }
    output = constrain(output, -500, 500); 
    //update for next iteration
    mixSources[mxr->output] = (int16_t) output;
  }
  
  ///----------------- OUTPUT TO CHANNELS ----------------
  
  for(uint8_t i = 0; i < NUM_RC_CHANNELS; i++)
  {
    channelOut[i] = mixSources[SRC_CH1 + i];
    //curve
    if(Model.Channel[i].curve != -1)
    {
      uint8_t _crvIdx = Model.Channel[i].curve;
      uint8_t _numPts = Model.CustomCurve[_crvIdx].numPoints;
      int16_t _xx[MAX_NUM_POINTS_CUSTOM_CURVE];
      int16_t _yy[MAX_NUM_POINTS_CUSTOM_CURVE];
      for(uint8_t pt = 0; pt < _numPts; pt++)
      {
        _xx[pt] = 5 * Model.CustomCurve[_crvIdx].xVal[pt];
        _yy[pt] = 5 * Model.CustomCurve[_crvIdx].yVal[pt];
      }
      if(Model.CustomCurve[_crvIdx].smooth)
        channelOut[i] = cubicHermiteInterpolate(_xx, _yy, _numPts, channelOut[i]);
      else
        channelOut[i] = linearInterpolate(_xx, _yy, _numPts, channelOut[i]);
    }
    //reverse
    if(Model.Channel[i].reverse) 
      channelOut[i] = 0 - channelOut[i]; 
    //subtrim
    channelOut[i] += 5 * Model.Channel[i].subtrim / 10; 
    //override
    if(Model.Channel[i].overrideSwitch != CTRL_SW_NONE && checkSwitchCondition(Model.Channel[i].overrideSwitch))
      channelOut[i] = 5 * Model.Channel[i].overrideVal;
    //endpoints
    int16_t endptL = 5 * Model.Channel[i].endpointL;
    int16_t endptR = 5 * Model.Channel[i].endpointR;
    channelOut[i] = constrain(channelOut[i], endptL, endptR); 
  }
  
  /// ---------------- RESET SOME VARIABLES --------------
  isReinitialiseMixer = false;
}

//==================================================================================================

void moveMix(uint8_t newPos, uint8_t oldPos)
{
  if(newPos >= NUM_MIX_SLOTS || oldPos >= NUM_MIX_SLOTS || newPos == oldPos)
    return;
  
  // store temporarily the old position's data
  mixer_params_t Temp_Mixer    = Model.Mixer[oldPos];
  int16_t  tempDlyOldVal       = dlyOldVal[oldPos];
  int8_t   tempDlyPrevOperand  = dlyPrevOperand[oldPos];
  uint8_t  tempDlyPrevInputIdx = dlyPrevInput[oldPos];
  uint32_t tempDlyStartTime    = dlyStartTime[oldPos];
  int32_t  tempSlowCurrVal     = slowCurrVal[oldPos];
  int16_t  tempHldOldVal       = hldOldVal[oldPos];
  uint8_t  tempHldOldState     = hldOldState[oldPos];

  //shift elements of the arrays
  uint8_t thisPostn = oldPos;
  if(newPos < oldPos)
  {
    while(thisPostn > newPos)
    {
      Model.Mixer[thisPostn]     = Model.Mixer[thisPostn-1];
      dlyOldVal[thisPostn]       = dlyOldVal[thisPostn-1];
      dlyPrevOperand[thisPostn]  = dlyPrevOperand[thisPostn-1];
      dlyPrevInput[thisPostn]    = dlyPrevInput[thisPostn-1];
      dlyStartTime[thisPostn]    = dlyStartTime[thisPostn-1];
      slowCurrVal[thisPostn]     = slowCurrVal[thisPostn-1];
      hldOldVal[thisPostn]       = hldOldVal[thisPostn-1];
      hldOldState[thisPostn]     = hldOldState[thisPostn-1];
      
      thisPostn--;
    }
  }
  else if(newPos > oldPos) 
  {
    while(thisPostn < newPos)
    {
      Model.Mixer[thisPostn]     = Model.Mixer[thisPostn+1];
      dlyOldVal[thisPostn]       = dlyOldVal[thisPostn+1];
      dlyPrevOperand[thisPostn]  = dlyPrevOperand[thisPostn+1];
      dlyPrevInput[thisPostn]    = dlyPrevInput[thisPostn+1];
      dlyStartTime[thisPostn]    = dlyStartTime[thisPostn+1];
      slowCurrVal[thisPostn]     = slowCurrVal[thisPostn+1];
      hldOldVal[thisPostn]       = hldOldVal[thisPostn+1];
      hldOldState[thisPostn]     = hldOldState[thisPostn+1];
      
      thisPostn++;
    }
  }
  
  //copy from temporary into new position
  Model.Mixer[newPos]     = Temp_Mixer;
  dlyOldVal[newPos]       = tempDlyOldVal;
  dlyPrevOperand[newPos]  = tempDlyPrevOperand;
  dlyPrevInput[newPos]    = tempDlyPrevInputIdx;
  dlyStartTime[newPos]    = tempDlyStartTime;
  slowCurrVal[newPos]     = tempSlowCurrVal;
  hldOldVal[newPos]       = tempHldOldVal;
  hldOldState[newPos]     = tempHldOldState;
}

//==================================================================================================

void swapMix(uint8_t posA, uint8_t posB)
{
  if(posA >= NUM_MIX_SLOTS || posB >= NUM_MIX_SLOTS || posA == posB)
    return;
  
  //store posA to temp
  mixer_params_t Temp_Mixer    = Model.Mixer[posA];
  int16_t  tempDlyOldVal       = dlyOldVal[posA];
  int8_t   tempDlyPrevOperand  = dlyPrevOperand[posA];
  uint8_t  tempDlyPrevInputIdx = dlyPrevInput[posA];
  uint32_t tempDlyStartTime    = dlyStartTime[posA];
  int32_t  tempSlowCurrVal     = slowCurrVal[posA];
  int16_t  tempHldOldVal       = hldOldVal[posA];
  uint8_t  tempHldOldState     = hldOldState[posA];
  
  //copy posB to posA
  Model.Mixer[posA]     = Model.Mixer[posB];
  dlyOldVal[posA]       = dlyOldVal[posB];
  dlyPrevOperand[posA]  = dlyPrevOperand[posB];
  dlyPrevInput[posA]    = dlyPrevInput[posB];
  dlyStartTime[posA]    = dlyStartTime[posB];
  slowCurrVal[posA]     = slowCurrVal[posB];
  hldOldVal[posA]       = hldOldVal[posB];
  hldOldState[posA]     = hldOldState[posB];
  
  //copy from temp to posB
  Model.Mixer[posB]     = Temp_Mixer;
  dlyOldVal[posB]       = tempDlyOldVal;
  dlyPrevOperand[posB]  = tempDlyPrevOperand;
  dlyPrevInput[posB]    = tempDlyPrevInputIdx;
  dlyStartTime[posB]    = tempDlyStartTime;
  slowCurrVal[posB]     = tempSlowCurrVal;
  hldOldVal[posB]       = tempHldOldVal;
  hldOldState[posB]     = tempHldOldState;
}

//==================================================================================================

bool moveLogicalSwitch(uint8_t newPos, uint8_t oldPos)
{
  if(newPos >= NUM_LOGICAL_SWITCHES || oldPos >= NUM_LOGICAL_SWITCHES)
    return false;

  if(newPos == oldPos)
    return true;

  //--- Update all references of the affected logical switches

  //Try finding an unreferenced logical switch, so we can use it as temporary place holder, with
  //condition that it should lie outside of the range of newPos and oldPos.
  uint8_t freeLS = 0xFF;
  for(uint8_t i = 0; i < NUM_LOGICAL_SWITCHES; i++)
  {
    if(!changeLSReference(i, i) && Model.LogicalSwitch[i].func == LS_FUNC_NONE)
    {
      if((newPos < oldPos && (i > oldPos || i < newPos)) || (newPos > oldPos && (i > newPos || i < oldPos)))
      {
        freeLS = i;
        break;
      }
    }
  }

  //exit if not found
  if(freeLS == 0xFF)
    return false;

  //change the oldPos reference to that of the place holder
  changeLSReference(freeLS, oldPos);

  //change references
  if(newPos < oldPos)
  {
    for(int8_t pos = oldPos - 1; pos >= newPos; pos--)
      changeLSReference(pos + 1, pos);
  }
  else if(newPos > oldPos) 
  {
    for(int8_t pos = oldPos; pos < newPos; pos++)
      changeLSReference(pos, pos + 1);
  }

  //change reference from that of the place holder to that of the newPos
  changeLSReference(newPos, freeLS);
  
  //--- Move the array elements

  // store temporarily the old position's data
  logical_switch_t Temp_LogicalSwitch = Model.LogicalSwitch[oldPos];
  bool     tempLsDlyStarted           = lsDlyStarted[oldPos];
  uint32_t tempLsDlyStartTime         = lsDlyStartTime[oldPos];
  bool     tempLsDurOldState          = lsDurOldState[oldPos];
  uint32_t tempLsDurEndTime           = lsDurEndTime[oldPos];
  bool     tempLsToggleLastState      = lsToggleLastState[oldPos];
  int32_t  tempLsDeltaPrevVal         = lsDeltaPrevVal[oldPos];
  uint8_t  tempLsDeltaPrevInput       = lsDeltaPrevInput[oldPos];
  bool     tempLogicalSwitchState     = logicalSwitchState[oldPos];

  //shift elements of the arrays
  uint8_t thisPostn = oldPos;
  if(newPos < oldPos)
  {
    while(thisPostn > newPos)
    {
      Model.LogicalSwitch[thisPostn] = Model.LogicalSwitch[thisPostn-1];
      lsDlyStarted[thisPostn]        = lsDlyStarted[thisPostn-1];
      lsDlyStartTime[thisPostn]      = lsDlyStartTime[thisPostn-1];
      lsDurOldState[thisPostn]       = lsDurOldState[thisPostn-1];
      lsDurEndTime[thisPostn]        = lsDurEndTime[thisPostn-1];
      lsToggleLastState[thisPostn]   = lsToggleLastState[thisPostn-1];
      lsDeltaPrevVal[thisPostn]      = lsDeltaPrevVal[thisPostn-1];
      lsDeltaPrevInput[thisPostn]    = lsDeltaPrevInput[thisPostn-1];
      logicalSwitchState[thisPostn]  = logicalSwitchState[thisPostn-1];

      thisPostn--;
    }
  }
  else if(newPos > oldPos) 
  {
    while(thisPostn < newPos)
    {
      Model.LogicalSwitch[thisPostn] = Model.LogicalSwitch[thisPostn+1];
      lsDlyStarted[thisPostn]        = lsDlyStarted[thisPostn+1];
      lsDlyStartTime[thisPostn]      = lsDlyStartTime[thisPostn+1];
      lsDurOldState[thisPostn]       = lsDurOldState[thisPostn+1];
      lsDurEndTime[thisPostn]        = lsDurEndTime[thisPostn+1];
      lsToggleLastState[thisPostn]   = lsToggleLastState[thisPostn+1];
      lsDeltaPrevVal[thisPostn]      = lsDeltaPrevVal[thisPostn+1];
      lsDeltaPrevInput[thisPostn]    = lsDeltaPrevInput[thisPostn+1];
      logicalSwitchState[thisPostn]  = logicalSwitchState[thisPostn+1];

      thisPostn++;
    }
  }

  //copy from temporary into new position
  Model.LogicalSwitch[newPos] = Temp_LogicalSwitch;
  lsDlyStarted[newPos]        = tempLsDlyStarted;
  lsDlyStartTime[newPos]      = tempLsDlyStartTime;
  lsDurOldState[newPos]       = tempLsDurOldState;
  lsDurEndTime[newPos]        = tempLsDurEndTime;
  lsToggleLastState[newPos]   = tempLsToggleLastState;
  lsDeltaPrevVal[newPos]      = tempLsDeltaPrevVal;
  lsDeltaPrevInput[newPos]    = tempLsDeltaPrevInput;
  logicalSwitchState[newPos]  = tempLogicalSwitchState;

  return true;
}

//==================================================================================================

void evaluateLogicalSwitches(uint32_t _currTime)
{
  if(isReinitialiseMixer)
  {
    for(uint8_t idx = 0; idx < NUM_LOGICAL_SWITCHES; idx++)
    {
      lsDlyStarted[idx] = false;
      lsDurOldState[idx] = false;
      logical_switch_t *ls = &Model.LogicalSwitch[idx]; 
      if(ls->func == LS_FUNC_TOGGLE)
        lsToggleLastState[idx] = checkSwitchCondition(ls->val1);
      if(ls->func == LS_FUNC_ABS_DELTA_GREATER_THAN_X)
        lsDeltaPrevInput[idx] = 0xFF;
    }
  }
    
  for(uint8_t idx = 0; idx < NUM_LOGICAL_SWITCHES; idx++)
  {
    logical_switch_t *ls = &Model.LogicalSwitch[idx];
    
    bool result = false;
    
    switch(ls->func)
    {
      case LS_FUNC_A_GREATER_THAN_X:
      case LS_FUNC_A_LESS_THAN_X:
      case LS_FUNC_A_EQUAL_X:
      case LS_FUNC_A_GREATER_THAN_OR_EQUAL_X:
      case LS_FUNC_A_LESS_THAN_OR_EQUAL_X:
      case LS_FUNC_ABS_A_GREATER_THAN_X:
      case LS_FUNC_ABS_A_LESS_THAN_X:
      case LS_FUNC_ABS_A_EQUAL_X:
      case LS_FUNC_ABS_A_GREATER_THAN_OR_EQUAL_X:
      case LS_FUNC_ABS_A_LESS_THAN_OR_EQUAL_X:
      case LS_FUNC_ABS_DELTA_GREATER_THAN_X:
        {
          int32_t _val1 = 0, _val2 = 0;
          if(ls->val1 < MIX_SOURCES_COUNT) //mix sources
          {
            _val1 = mixSources[ls->val1];
            _val2 = 5 * ls->val2;
          }
          else if(ls->val1 >= SRC_COUNTER_FIRST && ls->val1 <= SRC_COUNTER_LAST) //counters
          {
            _val1 = counterOut[ls->val1 - SRC_COUNTER_FIRST];
            _val2 = ls->val2;
          }
          else if(ls->val1 >= SRC_TIMER_FIRST && ls->val1 <= SRC_TIMER_LAST) //timers
          {
            uint8_t tmrIdx = ls->val1 - SRC_TIMER_FIRST;
            if(Model.Timer[tmrIdx].initialSeconds == 0) //a count up timer
            {
              _val1 = timerElapsedTime[tmrIdx];
            }
            else //count down timer
            {
              _val1 = (int32_t)Model.Timer[tmrIdx].initialSeconds * 1000;
              _val1 -= timerElapsedTime[tmrIdx];
            }
            _val2 = (int32_t)ls->val2 * 1000;
          }
          else if(ls->val1 >= SRC_TELEMETRY_FIRST && ls->val1 <= SRC_TELEMETRY_LAST)//telemetry
          {
            uint8_t tlmIdx = ls->val1 - SRC_TELEMETRY_FIRST;
            if(telemetryReceivedValue[tlmIdx] == TELEMETRY_NO_DATA)
              break; 
            else
            {
              _val1 = ((int32_t) telemetryReceivedValue[tlmIdx] * Model.Telemetry[tlmIdx].multiplier) / 100;
              _val1 += Model.Telemetry[tlmIdx].offset;
              _val2 = ls->val2;
            }
          }
          else if(ls->val1 == SRC_INACTIVITY_TIMER)
          {
            // _val1 = _currTime - inputsLastMovedTime;
            _val1 = millis() - inputsLastMovedTime;
            _val2 = (int32_t)ls->val2 * 1000;
          }
          else if(ls->val1 == SRC_TX_BATTERY_VOLTAGE)
          {
            _val1 = batteryVoltsNow;
            _val2 = ls->val2;
          }
          
          if(ls->func == LS_FUNC_A_GREATER_THAN_X)                result = _val1 > _val2;
          else if(ls->func == LS_FUNC_A_LESS_THAN_X)              result = _val1 < _val2;
          else if(ls->func == LS_FUNC_A_EQUAL_X)                  result = _val1 == _val2;
          else if(ls->func == LS_FUNC_A_GREATER_THAN_OR_EQUAL_X)  result = _val1 >= _val2;
          else if(ls->func == LS_FUNC_A_LESS_THAN_OR_EQUAL_X)     result = _val1 <= _val2;
          else if(ls->func == LS_FUNC_ABS_A_GREATER_THAN_X)       result = abs(_val1) > _val2;
          else if(ls->func == LS_FUNC_ABS_A_LESS_THAN_X)          result = abs(_val1) < _val2;
          else if(ls->func == LS_FUNC_ABS_A_EQUAL_X)              result = abs(_val1) == _val2;
          else if(ls->func == LS_FUNC_ABS_A_GREATER_THAN_OR_EQUAL_X) result = abs(_val1) >= _val2;
          else if(ls->func == LS_FUNC_ABS_A_LESS_THAN_OR_EQUAL_X) result = abs(_val1) <= _val2;
          else if(ls->func == LS_FUNC_ABS_DELTA_GREATER_THAN_X)
          {
            if(lsDeltaPrevInput[idx] != ls->val1) //reinitialise
            {
              lsDeltaPrevInput[idx] = ls->val1;
              lsDeltaPrevVal[idx] = _val1;
            }

            int32_t difference = _val1 - lsDeltaPrevVal[idx];
            if(abs(difference) > _val2)
            {
              if(ls->val3 == 0) //only in positive direction
              {
                if(difference > _val2)
                  result = true;
                if(result || difference < 0)
                  lsDeltaPrevVal[idx] = _val1;
              }
              else if(ls->val3 == 1) //only in negative direction
              {
                if(difference < -_val2)
                  result = true;
                if(result || difference > 0)
                  lsDeltaPrevVal[idx] = _val1;
              }
              else //both directions
              {
                result = true;
                lsDeltaPrevVal[idx] = _val1;
              }
            }
          }
        }
        break;

      case LS_FUNC_A_GREATER_THAN_B:
        result = mixSources[ls->val1] > mixSources[ls->val2];
        break;
      
      case LS_FUNC_A_LESS_THAN_B:
        result = mixSources[ls->val1] < mixSources[ls->val2];
        break;
        
      case LS_FUNC_A_EQUAL_B:
        result = mixSources[ls->val1] == mixSources[ls->val2];
        break;
        
      case LS_FUNC_A_GREATER_THAN_OR_EQUAL_B:
        result = mixSources[ls->val1] >= mixSources[ls->val2];
        break;
        
      case LS_FUNC_A_LESS_THAN_OR_EQUAL_B:
        result = mixSources[ls->val1] <= mixSources[ls->val2];
        break;
        
      case LS_FUNC_AND:
        result = checkSwitchCondition(ls->val1) && checkSwitchCondition(ls->val2);
        break;
         
      case LS_FUNC_OR:
        result = checkSwitchCondition(ls->val1) || checkSwitchCondition(ls->val2);
        break;
        
      case LS_FUNC_XOR:
        result = checkSwitchCondition(ls->val1) != checkSwitchCondition(ls->val2);
        break;
        
      case LS_FUNC_LATCH:
        {
          bool _val1 = checkSwitchCondition(ls->val1);
          bool _val2 = checkSwitchCondition(ls->val2);
          if(_val1 && !_val2) result = true;       //set
          else if(!_val1 && _val2) result = false; //reset
          else result = logicalSwitchState[idx];   //no change
        }
        break;
        
      case LS_FUNC_TOGGLE:
        {
          //get the previous result
          result = logicalSwitchState[idx]; 
          //get the state of the switch, the source of our clock
          bool state = checkSwitchCondition(ls->val1);
          //toggle on the rising edge
          if(ls->val2 == 0) 
          {
            if(state && !lsToggleLastState[idx]) //went from low to high
            {
              lsToggleLastState[idx] = true;
              result = !logicalSwitchState[idx];
            }
            else if(!state)
              lsToggleLastState[idx] = false;
          }
          //toggle on falling edge
          if(ls->val2 == 1) 
          {
            if(!state && lsToggleLastState[idx]) //went from high to low
            {
              lsToggleLastState[idx] = false;
              result = !logicalSwitchState[idx];
            }
            else if(state)
              lsToggleLastState[idx] = true;
          }
          //dual edge triggering i.e. both rising and falling edges
          if(ls->val2 == 2)
          {
            if(state != lsToggleLastState[idx])
            {
              lsToggleLastState[idx] = state;
              result = !logicalSwitchState[idx];
            }
          }
          
          //clear. This overrides result to false.
          if(ls->val3 != CTRL_SW_NONE && checkSwitchCondition(ls->val3))
            result = false;
        }
        break;
        
      case LS_FUNC_PULSE:
        {
          uint32_t highTime   = (uint32_t)ls->val1 * 100;
          uint32_t period     = (uint32_t)ls->val2 * 100;
          uint32_t pulseDelay = (uint32_t)ls->val3 * 100;
          uint32_t timeInstance;
          //As we are dealing with unsigned subtraction, we need to prevent strange results here
          //because at start up, the value of _currTime is less than that of pulseDelay.
          if(_currTime >= pulseDelay)
            timeInstance = (_currTime - pulseDelay) % period;
          else
          {
            timeInstance = period - ((pulseDelay - _currTime) % period); 
            timeInstance %= period;
          }
          result = timeInstance < highTime;
        }
        break;
    }
    
    //delay
    //here we delay activation of the logical switch by overriding for the specified time
    if(ls->val3 > 0)
    {
      if(ls->func != LS_FUNC_NONE 
         && ls->func != LS_FUNC_PULSE 
         && ls->func != LS_FUNC_TOGGLE 
         && ls->func != LS_FUNC_ABS_DELTA_GREATER_THAN_X)
      {
        if(result && !logicalSwitchState[idx]) //went from false to true
        {
          if(!lsDlyStarted[idx])
          {
            lsDlyStartTime[idx] = _currTime;
            lsDlyStarted[idx] = true;
          }
        }
        if(!result) //reset flag
          lsDlyStarted[idx] = false;
          
        if(_currTime - lsDlyStartTime[idx] < ((uint32_t)ls->val3 * 100)) //override result
          result = false;
      }
      else
      {
        lsDlyStarted[idx] = false;
      }
    }
    
    //duration
    if(ls->val4 > 0)
    {
      if(ls->func != LS_FUNC_NONE 
         && ls->func != LS_FUNC_PULSE 
         && ls->func != LS_FUNC_LATCH 
         && ls->func != LS_FUNC_TOGGLE)
      {
        if(result && !lsDurOldState[idx]) //went from inactive to active
        {
          lsDurOldState[idx] = true;
          lsDurEndTime[idx] = _currTime + ((uint32_t)ls->val4 * 100); 
        }
        if(_currTime >= lsDurEndTime[idx]) //duration has expired
        {
          if(!result) //only reset old state when result goes false
            lsDurOldState[idx] = false;
          result = false;
        }
        else if(lsDurOldState[idx]) //hold even if the input suddenly became false before duration expired
          result = true;
      }
      else
      {
        lsDurOldState[idx] = false;
      }
    }

    //store the result
    logicalSwitchState[idx] = result;
  }
}

//==================================================================================================

void evaluateCounters()
{
  static union {
    bool counterToggleLastState[NUM_COUNTERS];
    bool counterIncToggleLastState[NUM_COUNTERS];
  };
  static bool counterDecToggleLastState[NUM_COUNTERS];

  for(uint8_t idx = 0; idx < NUM_COUNTERS; idx++)
  {
    counter_params_t *counter = &Model.Counter[idx];
    
    if(isReinitialiseMixer)
    {
      if(counter->type == COUNTER_TYPE_BASIC)
        counterToggleLastState[idx] = checkSwitchCondition(counter->clock);
      else if(counter->type == COUNTER_TYPE_ADVANCED)
      {
        counterIncToggleLastState[idx] = checkSwitchCondition(counter->incrementClock);
        counterDecToggleLastState[idx] = checkSwitchCondition(counter->decrementClock);
      }
      continue;
    }
    
    if(counter->type == COUNTER_TYPE_BASIC)
    {
      bool state = (counter->clock != CTRL_SW_NONE) ? checkSwitchCondition(counter->clock) : false;
      if(counter->edge == 0) //on the rising edge
      {
        if(state && !counterToggleLastState[idx]) //went from low to high
        {
          counterToggleLastState[idx] = true;
          if(counter->direction == 0) 
            counterOut[idx]++;
          else 
            counterOut[idx]--;
        }
        else if(!state)
          counterToggleLastState[idx] = false;
      }
      else if(counter->edge == 1) //on falling edge
      {
        if(!state && counterToggleLastState[idx]) //went from high to low
        {
          counterToggleLastState[idx] = false;
          if(counter->direction == 0) 
            counterOut[idx]++;
          else 
            counterOut[idx]--;
        }
        else if(state)
          counterToggleLastState[idx] = true;
      }
      else if(counter->edge == 2) //dual edge triggering i.e. both rising and falling edges
      {
        if(state != counterToggleLastState[idx])
        {
          counterToggleLastState[idx] = state;
          if(counter->direction == 0) 
            counterOut[idx]++;
          else 
            counterOut[idx]--;
        }
      }
    }
    else if(counter->type == COUNTER_TYPE_ADVANCED)
    {
      //--- increment ---
      bool state = (counter->incrementClock != CTRL_SW_NONE) ? checkSwitchCondition(counter->incrementClock) : false;
      if(counter->incrementEdge == 0) //on the rising edge
      {
        if(state && !counterIncToggleLastState[idx]) //went from low to high
        {
          counterIncToggleLastState[idx] = true;
          counterOut[idx]++;
        }
        else if(!state)
          counterIncToggleLastState[idx] = false;
      }
      else if(counter->incrementEdge == 1) //on falling edge
      {
        if(!state && counterIncToggleLastState[idx]) //went from high to low
        {
          counterIncToggleLastState[idx] = false;
          counterOut[idx]++;
        }
        else if(state)
          counterIncToggleLastState[idx] = true;
      }
      else if(counter->incrementEdge == 2) //dual edge triggering i.e. both rising and falling edges
      {
        if(state != counterIncToggleLastState[idx])
        {
          counterIncToggleLastState[idx] = state;
          counterOut[idx]++;
        }
      }
      //--- decrement ---
      state = (counter->decrementClock != CTRL_SW_NONE) ? checkSwitchCondition(counter->decrementClock) : false;
      if(counter->decrementEdge == 0) //on the rising edge
      {
        if(state && !counterDecToggleLastState[idx]) //went from low to high
        {
          counterDecToggleLastState[idx] = true;
          counterOut[idx]--;
        }
        else if(!state)
          counterDecToggleLastState[idx] = false;
      }
      else if(counter->decrementEdge == 1) //on falling edge
      {
        if(!state && counterDecToggleLastState[idx]) //went from high to low
        {
          counterDecToggleLastState[idx] = false;
          counterOut[idx]--;
        }
        else if(state)
          counterDecToggleLastState[idx] = true;
      }
      else if(counter->decrementEdge == 2) //dual edge triggering i.e. both rising and falling edges
      {
        if(state != counterDecToggleLastState[idx])
        {
          counterDecToggleLastState[idx] = state;
          counterOut[idx]--;
        }
      }
    }
    
    //check against modulus
    if(counter->rolloverEnabled)
    {
      if(counterOut[idx] >= counter->modulus) 
        counterOut[idx] = 0;
      if(counterOut[idx] < 0)                 
        counterOut[idx] = counter->modulus - 1;
    }
    else
    {
      if(counterOut[idx] >= counter->modulus) 
        counterOut[idx] = counter->modulus - 1;
      if(counterOut[idx] < 0)            
        counterOut[idx] = 0;
    }
    
    //clear
    if(counter->clear != CTRL_SW_NONE && checkSwitchCondition(counter->clear))
      counterOut[idx] = 0;

    //store the register value
    counter->persistVal = (counter->isPersistent) ? counterOut[idx] : 0;
  }
}

//==================================================================================================

int16_t calcRateExpo(int16_t input, int16_t rate, int16_t expo)
{
  /* This function is for applying rate and cubic 'expo' to aileron, elevator and rudder.
     Ranges: input -500 to 500, rate 0 to 100, expo -100 to 100. 0 is linear
  */
  return ((int32_t)rate * calcExpo(input, expo)) / 100;
}

//==================================================================================================

int16_t calcExpo(int16_t input, int16_t expo)
{
  //Range: expo -100 to 100. 0 is linear, input -500 to 500
  
  /*
  The original equation is 
  y = e^(k*ln(x)) which simplifies to y = x^k
  However this is quite hard to compute on a simple microcontroller, therefore we use a cubic equation 
  that gives comparable results for the range we are interested in. 
  y = k*x^3 + (1-k)*x   where k is 'expo' factor. k range -1 to 1, x range -1 to 1
  
  For our implementation, we only use the range 0 < k < 1 and simply mirror the result if k is negative.
  We also work with only positive input in the calculation and simply negate the result for negative input.
  
  We need to scale up the above equation to avoid floating point math. After calculation, we scale back the result. 
  Thus the modified equation taking into account the range of our parameters is as follows. 
  y/500 = ((k/100)*(x/500)^3) + ((1-(k/100))*(x/500))
  
  Simplifying and rearranging to ensure no overflow for our range of values,
  y = (((k*x*x + 250000*(100-k))/250000)*x)/100
  */
  
  if(expo == 0)
    return input;

  int32_t x = abs(input);
  int32_t k = abs(expo);
  if(expo < 0)
    x -= 500;
  
  int32_t y = k*x*x + 250000*(100-k);
  y /= 250000;
  y *= x;
  y /= 100;
  
  if(expo < 0)
    y += 500;
  if(input < 0)
    y = -y;
  
  return (int16_t) y;
}

//==================================================================================================

int16_t calcDifferential(int16_t input, int16_t diff)
{
  int32_t output = input;
  if(diff > 0 && input < 0)
  {
    output *= (100 - diff);
    output /= 100;
  }
  else if(diff < 0 && input > 0)
  {
    output *= (100 + diff);
    output /= 100;
  }
 
  return (int16_t) output;
}

//==================================================================================================

int32_t applySlow(int32_t currVal, int32_t targetVal, int32_t range, int32_t multiplier, uint32_t riseTime, uint32_t fallTime)
{
  if(currVal < targetVal && riseTime > 0)
  {
    int32_t step = (multiplier * range * fixedLoopTime) / riseTime;
    currVal += step;
    if(currVal > targetVal)
      currVal = targetVal;
  }
  else if(currVal > targetVal && fallTime > 0) 
  {
    int32_t step = (multiplier * range * fixedLoopTime) / fallTime;
    currVal -= step;
    if(currVal < targetVal)
      currVal = targetVal;
  }
  else
    currVal = targetVal;
  
  return currVal;
}

//==================================================================================================

int16_t weightAndOffset(int16_t input, int16_t weight, int16_t offset)
{ 
  return (((int32_t)input * weight) / 100) + (offset * 5);
}

//==================================================================================================

bool checkSwitchCondition(uint8_t sw)
{
  bool result = false;
  
  if(sw == CTRL_SW_NONE) //always active
  {
    result = true;
  }
  else if(sw >= CTRL_SW_PHYSICAL_FIRST && sw <= CTRL_SW_PHYSICAL_LAST)
  {
    uint8_t idx = (sw - CTRL_SW_PHYSICAL_FIRST) / 6;
    uint8_t condition = (sw - CTRL_SW_PHYSICAL_FIRST) % 6;
    switch(condition) //up, mid, down, !up, !mid, !down
    {
      case 0: result = swState[idx] == SWUPPERPOS; break;
      case 1: result = swState[idx] == SWMIDPOS;   break; 
      case 2: result = swState[idx] == SWLOWERPOS; break;
      case 3: result = swState[idx] != SWUPPERPOS; break;
      case 4: result = swState[idx] != SWMIDPOS;   break;
      case 5: result = swState[idx] != SWLOWERPOS; break;
    }
  }
  else if(sw >= CTRL_SW_LOGICAL_FIRST && sw <= CTRL_SW_LOGICAL_LAST_INVERT)
  {
    bool invertResult = false;
    uint8_t idx = sw - CTRL_SW_LOGICAL_FIRST;
    if(sw >= CTRL_SW_LOGICAL_FIRST_INVERT)
    {
      idx = sw - CTRL_SW_LOGICAL_FIRST_INVERT;
      invertResult = true;
    }
    //check within array
    result = logicalSwitchState[idx];
    
    if(invertResult)
      result = !result;
  }
  else if(sw >= CTRL_SW_FMD_FIRST && sw <= CTRL_SW_FMD_LAST_INVERT)
  {
    bool invertResult = false;
    uint8_t fmdIdx = sw - CTRL_SW_FMD_FIRST;
    if(fmdIdx >= NUM_FLIGHT_MODES)
    {      
      fmdIdx -= NUM_FLIGHT_MODES;
      invertResult = true;
    }
    //compare with active flight mode
    if(fmdIdx == activeFmdIdx) 
      result = true;
    if(invertResult)
      result = !result;
  }
  else if(sw >= CTRL_SW_TRIM_FIRST && sw <= CTRL_SW_TRIM_LAST)
  {
    if(sw == CTRL_SW_X1_TRIM_LEFT && buttonCode == KEY_X1_TRIM_DOWN) result = true;
    else if(sw == CTRL_SW_X1_TRIM_RIGHT && buttonCode == KEY_X1_TRIM_UP) result = true;
    else if(sw == CTRL_SW_Y1_TRIM_UP && buttonCode == KEY_Y1_TRIM_UP) result = true;
    else if(sw == CTRL_SW_Y1_TRIM_DOWN && buttonCode == KEY_Y1_TRIM_DOWN) result = true;
    else if(sw == CTRL_SW_X2_TRIM_LEFT && buttonCode == KEY_X2_TRIM_DOWN) result = true;
    else if(sw == CTRL_SW_X2_TRIM_RIGHT && buttonCode == KEY_X2_TRIM_UP) result = true;
    else if(sw == CTRL_SW_Y2_TRIM_UP && buttonCode == KEY_Y2_TRIM_UP) result = true;
    else if(sw == CTRL_SW_Y2_TRIM_DOWN && buttonCode == KEY_Y2_TRIM_DOWN) result = true;
  }
  
  return result;
}

//==================================================================================================

int16_t adjustTrim(uint8_t idx, int16_t val, uint8_t incButton, uint8_t decButton)
{
  if(idx >= 4)
    return val;
  
  int16_t step = 0;

  enum {
    //the actual value should multiply well with our internal factor of 5
    STEP_VAL_COARSE = 20,  //2.0
    STEP_VAL_MEDIUM = 10,  //1.0
    STEP_VAL_FINE = 2,     //0.2
  };
  
  switch(Model.trimStep)
  {
    case TRIM_STEP_COARSE:  step = STEP_VAL_COARSE; break;   
    case TRIM_STEP_MEDIUM:  step = STEP_VAL_MEDIUM; break;  
    case TRIM_STEP_FINE:    step = STEP_VAL_FINE;  break;  
  }

  uint8_t _heldBtn = 0;
  uint8_t _repeatDelay = 200;
  if(millis() - buttonStartTime > (1000 + Sys.longPressDelay)) //speed up
  {
    _repeatDelay = 100;
    if((millis() - buttonStartTime > (3000 + Sys.longPressDelay)) && step == STEP_VAL_FINE)
      step = STEP_VAL_MEDIUM;
  }

  if((thisLoopNum - heldButtonEntryLoopNum) % (_repeatDelay / fixedLoopTime) == 0) 
    _heldBtn = heldButton;
  
  //briefly pause at the center
  static bool paused[4];
  static uint32_t pausedLoopNum[4];
  if(val == 0 && _heldBtn && !paused[idx])
  {
    paused[idx] = true;
    pausedLoopNum[idx] = thisLoopNum;
  }
  if(val != 0)
  {
    paused[idx] = false;
  }
  if(paused[idx])
  {
    if((thisLoopNum - pausedLoopNum[idx]) < ((uint32_t) Sys.longPressDelay / fixedLoopTime))
      _heldBtn = 0;
  }
  
  //adjust value
  if((pressedButton == decButton || _heldBtn == decButton))
  {    
    bool limitReached = false;
    val -= step;
    if(step == STEP_VAL_MEDIUM || step == STEP_VAL_COARSE)
    {
      if(abs(val) < STEP_VAL_MEDIUM) //snap to center
        val = 0;
    }
    if(val < TRIM_MIN_VAL)
    {
      val = TRIM_MIN_VAL;
      limitReached = true;
    }
    if(Sys.soundTrims)
    {
      if(!limitReached)
      {
        audioTrimVal = val;
        audioToPlay = AUDIO_TRIM_MOVED;
        if(val == 0)
          audioToPlay = AUDIO_TRIM_CENTERED;
      }
    }
  }
  else if((pressedButton == incButton || _heldBtn == incButton))
  {
    bool limitReached = false;
    val += step;
    if(step == STEP_VAL_MEDIUM || step == STEP_VAL_COARSE)
    {
      if(abs(val) < STEP_VAL_MEDIUM) //snap to center
        val = 0;
    }
    if(val > TRIM_MAX_VAL)
    {
      val = TRIM_MAX_VAL;
      limitReached = true;
    }
    if(Sys.soundTrims)
    {
      if(!limitReached)
      {
        audioTrimVal = val;
        audioToPlay = AUDIO_TRIM_MOVED;
        if(val == 0)
          audioToPlay = AUDIO_TRIM_CENTERED;
      }
    }
  }
  
  return val;
}

//==================================================================================================

bool isSyncWaveform[NUM_FUNCGEN];

void syncWaveform(uint8_t idx)
{
  if(idx >= NUM_FUNCGEN)
    return;
  isSyncWaveform[idx] = true;
}

int16_t generateWaveform(uint8_t idx, int32_t _currTime)
{
  if(idx >= NUM_FUNCGEN)
    return 0;
  
  int16_t result = 0;
  
  funcgen_t *fgen = &Model.Funcgen[idx];
  
  int32_t period;
  if(fgen->waveform == FUNCGEN_WAVEFORM_PULSE)
  {
    period = (int32_t)fgen->period * 100;
  }
  else
  {
    if(fgen->periodMode == FUNCGEN_PERIODMODE_FIXED)
      period = (int32_t)fgen->period1 * 100;
    else //variable period
    {
      int32_t m = fgen->reverseModulator ? 0 - mixSources[fgen->modulatorSrc] : mixSources[fgen->modulatorSrc];
      period = (((m + 500) * (fgen->period2 - fgen->period1)) / 10) + ((int32_t)fgen->period1 * 100);
    }
  }
  
  static int32_t oldPeriod[NUM_FUNCGEN];
  static int32_t timeOffset[NUM_FUNCGEN];
  
  int32_t timeInstance = 0; 
  
  if(isSyncWaveform[idx])
  {
    isSyncWaveform[idx] = false;
    timeOffset[idx] = 0;
  }

  bool phaseCompensate = false;
  
  if(fgen->waveform == FUNCGEN_WAVEFORM_PULSE)
  {
    if(fgen->phaseMode == FUNCGEN_PHASEMODE_AUTO)
      phaseCompensate = true;
  }
  else
  {
    if((fgen->periodMode == FUNCGEN_PERIODMODE_FIXED && fgen->phaseMode == FUNCGEN_PHASEMODE_AUTO) 
      || fgen->periodMode == FUNCGEN_PERIODMODE_VARIABLE)
    {
      phaseCompensate = true;
    }
  }

  if(phaseCompensate)
  {
    // Smoothly transition to new period when the period is being adjusted.
    // We add some time offset so that we maintain the next ratio of timeInstance/period upon change.
    if(period != oldPeriod[idx])
    {
      if(oldPeriod[idx] == 0) //at initial run
      {
        timeOffset[idx] = 0;
        oldPeriod[idx] = period; 
      }
      else
      {
        int32_t nextTimeInstance = (_currTime + timeOffset[idx]) % oldPeriod[idx];
        timeOffset[idx] = ((period * nextTimeInstance)/oldPeriod[idx]) - (_currTime % period);
        oldPeriod[idx] = period; 
      }
    }
    timeInstance = (_currTime + timeOffset[idx]) % period;
  }
  else //fixed phase
  {
    timeOffset[idx] = ((int32_t) fgen->phase * period) / 360;
    if(_currTime >= timeOffset[idx])
      timeInstance = (_currTime - timeOffset[idx]) % period;
    else
    {
      timeInstance = period - ((timeOffset[idx] - _currTime) % period); 
      timeInstance %= period;
    }
  }

  switch(fgen->waveform)
  {
    case FUNCGEN_WAVEFORM_SINE:
      {
        static const int16_t sineTable[256] PROGMEM = {
          0, 12, 25, 37, 49, 61, 73, 85, 98, 110, 121, 133, 145, 157, 168, 180,
          191, 203, 214, 225, 236, 246, 257, 267, 278, 288, 298, 308, 317, 327, 336, 345,
          354, 362, 370, 379, 387, 394, 402, 409, 416, 422, 429, 435, 441, 447, 452, 457,
          462, 466, 471, 475, 478, 482, 485, 488, 490, 493, 495, 496, 498, 499, 499, 500,
          500, 500, 499, 499, 498, 496, 495, 493, 490, 488, 485, 482, 478, 475, 471, 466,
          462, 457, 452, 447, 441, 435, 429, 422, 416, 409, 402, 394, 387, 379, 370, 362,
          354, 345, 336, 327, 317, 308, 298, 288, 278, 267, 257, 246, 236, 225, 214, 203,
          191, 180, 168, 157, 145, 133, 121, 110, 98, 85, 73, 61, 49, 37, 25, 12,
          0, -12, -25, -37, -49, -61, -73, -85, -98, -110, -121, -133, -145, -157, -168, -180,
          -191, -203, -214, -225, -236, -246, -257, -267, -278, -288, -298, -308, -317, -327, -336, -345,
          -354, -362, -370, -379, -387, -394, -402, -409, -416, -422, -429, -435, -441, -447, -452, -457,
          -462, -466, -471, -475, -478, -482, -485, -488, -490, -493, -495, -496, -498, -499, -499, -500,
          -500, -500, -499, -499, -498, -496, -495, -493, -490, -488, -485, -482, -478, -475, -471, -466,
          -462, -457, -452, -447, -441, -435, -429, -422, -416, -409, -402, -394, -387, -379, -370, -362,
          -354, -345, -336, -327, -317, -308, -298, -288, -278, -267, -257, -246, -236, -225, -214, -203,
          -191, -180, -168, -157, -145, -133, -121, -110, -98, -85, -73, -61, -49, -37, -25, -12
        };

        //--fixed point arithmetic with a fractional part
        // the fractional part is used for linear interpolation
        const int16_t multiplier = 32;
        int16_t index = (timeInstance * (sizeof(sineTable)/sizeof(sineTable[0])) * multiplier) / period; 
        uint16_t indexLUT = index / multiplier;
        int16_t valL = (int16_t)pgm_read_word(&sineTable[indexLUT]);
        indexLUT++;
        if(indexLUT >= (sizeof(sineTable)/sizeof(sineTable[0]))) 
          indexLUT = 0;
        int16_t valR = (int16_t)pgm_read_word(&sineTable[indexLUT]);
        result = valL + (((valR - valL)*(index % multiplier)) / multiplier);
      }
      break;
    
    case FUNCGEN_WAVEFORM_SAWTOOTH:
      {
        if(timeInstance < (period/2))
          result = map(timeInstance, 0, period/2, 0, 500);
        else
          result = map(timeInstance, period/2, period, -500, 0);
      }
      break;
    
    case FUNCGEN_WAVEFORM_TRIANGLE:
      {
        if(timeInstance < (period/4))
          result = map(timeInstance, 0, period/4, 0, 500);
        else if(timeInstance < ((3 * period)/4))
          result = map(timeInstance, period/4, (3 * period)/4, 500, -500);
        else
          result = map(timeInstance, (3 * period)/4, period, -500, 0);
      }
      break;
    
    case FUNCGEN_WAVEFORM_SQUARE:
      {
        result = timeInstance < (period/2) ? 500 : -500;
      }
      break;

    case FUNCGEN_WAVEFORM_PULSE:
      {
        if(fgen->widthMode == FUNCGEN_PULSE_WIDTH_FIXED)
          result = (timeInstance < ((int32_t)fgen->width * 100)) ? 500 : -500;
        else if(fgen->widthMode == FUNCGEN_PULSE_WIDTH_VARIABLE)
        {
          //duty cycle is only updated at the end of the PWM cycle to prevent glitches.
          static int32_t prevTimeInstance[NUM_FUNCGEN];
          static int16_t modulatorValue[NUM_FUNCGEN];
          if(timeInstance < prevTimeInstance[idx])
          {
            modulatorValue[idx] = mixSources[fgen->modulatorSrc];
            if(fgen->reverseModulator)
              modulatorValue[idx] = 0 - modulatorValue[idx];
          }
          prevTimeInstance[idx] = timeInstance;
          int32_t highTime = ((modulatorValue[idx] + 500) * period) / 1000;
          result = (timeInstance < highTime) ? 500 : -500;
        }
      }
      break;

    case FUNCGEN_WAVEFORM_RANDOM:
      {
        static bool isExpired[NUM_FUNCGEN];
        static int16_t lastResult[NUM_FUNCGEN];
        if(timeInstance < (period/2) && isExpired[idx])
        {
          isExpired[idx] = false;
          lastResult[idx] = random(-500, 500);
        }
        if(timeInstance >= (period/2))
          isExpired[idx] = true;
        
        result = lastResult[idx];
      }
      break;
  }
  
  result = constrain(result, -500, 500);
  return result;
}
