buk7456/FreeTX/source code/transmitter/mtx/src/inputs.cpp

#include "Arduino.h"

#include "../config.h"
#include "common.h"
#include "inputs.h"

int16_t deadzoneAndMap(int16_t input, int16_t minVal, int16_t centreVal, int16_t maxVal, int16_t deadzn, int16_t mapMin, int16_t mapMax);

const uint8_t swPin[NUM_PHYSICAL_SWITCHES][2] PROGMEM = {
  {PIN_SWA_UP, PIN_SWA_DN},
  {PIN_SWB_UP, PIN_SWB_DN},
  {PIN_SWC_UP, PIN_SWC_DN},
  {PIN_SWD_UP, PIN_SWD_DN},
  {PIN_SWE_UP, PIN_SWE_DN},
  {PIN_SWF_UP, PIN_SWF_DN},
  {PIN_SWG_UP, PIN_SWG_DN},
  {PIN_SWH_UP, PIN_SWH_DN}
};

const uint8_t stickAxisPin[NUM_STICK_AXES] PROGMEM = {
  PIN_X1_AXIS,
  PIN_Y1_AXIS,
  PIN_Z1_AXIS,
  PIN_X2_AXIS,
  PIN_Y2_AXIS,
  PIN_Z2_AXIS,
  PIN_X3_AXIS,
  PIN_Y3_AXIS,
  PIN_X4_AXIS,
  PIN_Y4_AXIS
};

const uint8_t knobPin[NUM_KNOBS] PROGMEM = {
  PIN_KNOB_A,
  PIN_KNOB_B
};

//==================================================================================================

void initialiseSwitches()
{
  for(uint8_t i = 0; i < NUM_PHYSICAL_SWITCHES; i++)
  {
    pinMode(pgm_read_byte(&swPin[i][0]), INPUT_PULLUP);
    pinMode(pgm_read_byte(&swPin[i][1]), INPUT_PULLUP);
  }
}

//==================================================================================================

void readSwitchesAndButtons()
{
  //--Read switches--
  //These are read on every other call to the function, as an extra debounce measure,
  //at the expense of slight additional delay/lag.
  static bool read;
  read = !read;
  if(read)
  {
    for(uint8_t i = 0; i < NUM_PHYSICAL_SWITCHES; i++)
    {
      swState[i] = SWUPPERPOS;
      if(Sys.swType[i] == SW_2POS || Sys.swType[i] == SW_2POS_MOMENTARY) 
      {
        if(!digitalRead(pgm_read_byte(&swPin[i][1]))) 
          swState[i] = SWLOWERPOS;
      }
      else if(Sys.swType[i] == SW_3POS || Sys.swType[i] == SW_3POS_MOMENTARY) 
      {
        swState[i] = SWMIDPOS;
        if(!digitalRead(pgm_read_byte(&swPin[i][0])))      
          swState[i] = SWUPPERPOS;
        else if(!digitalRead(pgm_read_byte(&swPin[i][1]))) 
          swState[i] = SWLOWERPOS;
      }
    }
  }

  //--Read trims and UI buttons--
  //Only one button can be pressed at a time
  
  buttonCode = 0;

  if(!(PINx_TRIMS & 0x80)) buttonCode = KEY_X2_TRIM_UP;
  if(!(PINx_TRIMS & 0x40)) buttonCode = KEY_X2_TRIM_DOWN;
  if(!(PINx_TRIMS & 0x20)) buttonCode = KEY_Y2_TRIM_UP;
  if(!(PINx_TRIMS & 0x10)) buttonCode = KEY_Y2_TRIM_DOWN;
  if(!(PINx_TRIMS & 0x08)) buttonCode = KEY_Y1_TRIM_UP;
  if(!(PINx_TRIMS & 0x04)) buttonCode = KEY_Y1_TRIM_DOWN;
  if(!(PINx_TRIMS & 0x02)) buttonCode = KEY_X1_TRIM_UP;
  if(!(PINx_TRIMS & 0x01)) buttonCode = KEY_X1_TRIM_DOWN;

  if(!digitalRead(PIN_KEY_SELECT)) buttonCode = KEY_SELECT;
  if(!digitalRead(PIN_KEY_UP))     buttonCode = KEY_UP;
  if(!digitalRead(PIN_KEY_DOWN))   buttonCode = KEY_DOWN;

  if(buttonCode != 0)
    inputsLastMovedTime = millis();
  
  //-- play audio when switches are moved --
  static uint8_t lastSwState[NUM_PHYSICAL_SWITCHES];
  static bool initialised = false;
  if(!initialised)
  {
    initialised = true;
    for(uint8_t i = 0; i < NUM_PHYSICAL_SWITCHES; i++)
      lastSwState[i] = swState[i];
  }
  bool beep = false;
  for(uint8_t i = 0; i < NUM_PHYSICAL_SWITCHES; i++)
  {
    if(swState[i] != lastSwState[i])
    {
      if(Sys.swType[i] == SW_2POS || Sys.swType[i] == SW_3POS)
        beep = true;
      else if(Sys.swType[i] == SW_2POS_MOMENTARY && swState[i] == SWLOWERPOS)
        beep = true;
      else if(Sys.swType[i] == SW_3POS_MOMENTARY && swState[i] != SWMIDPOS)
        beep = true;
      lastSwState[i] = swState[i];
      inputsLastMovedTime = millis(); 
    }
  }
  if(beep && Sys.soundSwitches)
    audioToPlay = AUDIO_SWITCH_MOVED;
}

//==================================================================================================

static bool buttonActive = false;
static uint8_t lastButtonCode = 0;
static bool buttonEventsOverridden = false;

void determineButtonEvent()
{
  /* 
  Modifies the pressedButton, clickedButton and heldButton variables, buttonStartTime 
  and buttonReleaseTime.
  Events
  - pressedButton is triggered once when the button goes down
  - clickedButton is triggered when the button is released before heldButton event
  - heldButton is triggered when button is held down long enough  
  */
  
  if(buttonEventsOverridden)
  {
    if(buttonActive)
    {
      buttonActive = false;
      buttonReleaseTime = millis();
    }
    //suppress until buttons are released
    if(buttonCode == 0)
      buttonEventsOverridden = false;
    else
      return;
  }

  //clear pressed and clicked events
  pressedButton = 0;
  clickedButton = 0;
  
  //button just went down
  if(buttonCode > 0 && !buttonActive && (millis() - buttonReleaseTime > 100)) 
  {
    buttonActive = true;
    buttonStartTime = millis();
    pressedButton = buttonCode;  //event
    lastButtonCode = buttonCode; //store the buttonCode
    //play audio
    if(buttonCode >= KEY_TRIM_FIRST && buttonCode <= KEY_TRIM_LAST) //Trim buttons
    {
      if(Sys.soundSwitches)
      {
        //treat as generic switches if the corresponding trim is disabled
        if(Model.X1Trim.trimState == TRIM_DISABLED && (buttonCode == KEY_X1_TRIM_DOWN || buttonCode == KEY_X1_TRIM_UP))
          audioToPlay = AUDIO_SWITCH_MOVED;
        if(Model.Y1Trim.trimState == TRIM_DISABLED && (buttonCode == KEY_Y1_TRIM_DOWN || buttonCode == KEY_Y1_TRIM_UP))
          audioToPlay = AUDIO_SWITCH_MOVED;
        if(Model.X2Trim.trimState == TRIM_DISABLED && (buttonCode == KEY_X2_TRIM_DOWN || buttonCode == KEY_X2_TRIM_UP))
          audioToPlay = AUDIO_SWITCH_MOVED;
        if(Model.Y2Trim.trimState == TRIM_DISABLED && (buttonCode == KEY_Y2_TRIM_DOWN || buttonCode == KEY_Y2_TRIM_UP))
          audioToPlay = AUDIO_SWITCH_MOVED;
      }
    }
    else if(Sys.soundKeys) //UI navigation buttons
      audioToPlay = AUDIO_KEY_PRESSED;
  }
  
  //button is down long enough, trigger heldButton event
  static bool heldButtonActive = false;
  if(buttonActive && (millis() - buttonStartTime > Sys.longPressDelay))
  {
    heldButton = lastButtonCode; //event
    if(!heldButtonActive)
    {
      heldButtonActive = true;
      heldButtonEntryLoopNum = thisLoopNum; //record the loop number at which it first occurred
    }
  }
  
  //button has just been released
  if(buttonCode == 0 && buttonActive)
  {
    buttonActive = false;
    buttonReleaseTime = millis();
    
    //trigger clickedButton event if there was no heldButton
    if(heldButton == 0) 
      clickedButton = lastButtonCode; //event
    
    //clear heldButton event and associated variables
    heldButton = 0; 
    heldButtonActive = false;
  }
}

//==================================================================================================

void killButtonEvents()
{
  pressedButton = 0;
  clickedButton = 0;
  heldButton = 0;
  buttonEventsOverridden = true;
}

//==================================================================================================

void readSticks()
{
  if(isCalibratingControls)
    return;

  //Read stick axes
  for(uint8_t i = 0; i < NUM_STICK_AXES; i++)
  {
    stick_axis_params_t *axis = &Sys.StickAxis[i];
    if(axis->type == STICK_AXIS_ABSENT)
      stickAxisIn[i] = 0;
    else
    {
      stickAxisIn[i] = analogRead(pgm_read_byte(&stickAxisPin[i]));
      if(axis->type == STICK_AXIS_SELF_CENTERING)
      {
        stickAxisIn[i] = deadzoneAndMap(stickAxisIn[i], axis->minVal, axis->centerVal, axis->maxVal, 
                                        axis->deadzone, -500, 500);
      }
      else if(axis->type == STICK_AXIS_NON_CENTERING)
      {
        stickAxisIn[i] = map(stickAxisIn[i], axis->minVal, axis->maxVal, -500, 500);
        stickAxisIn[i] = constrain(stickAxisIn[i], -500, 500);
      }
    }
  }

  //Read knobs
  for(uint8_t i = 0; i < NUM_KNOBS; i++)
  {
    knob_params_t *knob = &Sys.Knob[i];
    if(knob->type == KNOB_ABSENT)
      knobIn[i] = 0;
    else
    {
      knobIn[i] = analogRead(pgm_read_byte(&knobPin[i]));
      if(knob->type == KNOB_CENTER_DETENT)
      {
        knobIn[i] = deadzoneAndMap(knobIn[i], knob->minVal, knob->centerVal, knob->maxVal, 
                                   knob->deadzone, -500, 500);
      }
      else if(knob->type == KNOB_NO_CENTER_DETENT)
      {
        knobIn[i] = map(knobIn[i], knob->minVal, knob->maxVal, -500, 500); 
        knobIn[i] = constrain(knobIn[i], -500, 500);
      }
    }
  }

  //play audio whenever a knob is at the center
  enum {
    CENTER = 0,
    NEG_SIDE,
    POS_SIDE, 
  };
  static uint8_t knobRegion[NUM_KNOBS];
  for(uint8_t i = 0; i < NUM_KNOBS; i++)
  {
    if((knobIn[i] >= 0 && knobRegion[i] == NEG_SIDE) || (knobIn[i] <= 0 && knobRegion[i] == POS_SIDE))
    {
      knobRegion[i] = CENTER;
      if(Sys.soundKnobCenter)
        audioToPlay = AUDIO_KNOB_CENTERED;
    }
    else if(knobIn[i] > 25) 
      knobRegion[i] = POS_SIDE;
    else if(knobIn[i] < -25) 
      knobRegion[i] = NEG_SIDE;
  }

  //Detect inactivity
  static int16_t lastSum = 0;
  int16_t sum = 0;
  for(uint8_t i = 0; i < NUM_STICK_AXES; i++)
    sum += stickAxisIn[i];
  for(uint8_t i = 0; i < NUM_KNOBS; i++)
    sum += knobIn[i];
  if(abs(sum - lastSum) > 50) //5% of 1000
  {
    lastSum = sum;
    inputsLastMovedTime = millis();
  }
}

//====================================Helpers=======================================================

int16_t deadzoneAndMap(int16_t input, int16_t minVal, int16_t centreVal, int16_t maxVal, int16_t deadzn, int16_t mapMin, int16_t mapMax)
{
  //Formula is ((maxVal-minVal)*deadzn/100)/2. We divide by 2 as it is applied about center
  int16_t deadznVal = ((int32_t)(maxVal - minVal) * deadzn) / 200;
  int16_t threshR = centreVal + deadznVal;
  int16_t threshL = centreVal - deadznVal;
  int16_t mapCenter = (mapMin + mapMax) / 2;
  int16_t output = mapCenter;
  if(input > threshR)
    output = map(input, threshR, maxVal, mapCenter + 1, mapMax);
  else if(input < threshL)
    output = map(input, minVal, threshL, mapMin, mapCenter - 1);
  output = constrain(output, mapMin, mapMax);
  return output;
}

//==================================================================================================

void calibrateSticks(uint8_t stage)
{
  switch(stage)
  {
    case CALIBRATE_INIT:
    {
      //set min to highest and max to lowest
      for(uint8_t i = 0; i < NUM_STICK_AXES; i++)
      {
        Sys.StickAxis[i].minVal = 1023;
        Sys.StickAxis[i].maxVal = 0;
      }
    }
    break;
    
    case CALIBRATE_MOVE:
    {
      //get min, max, center
      int16_t reading;
      for(uint8_t i = 0; i < NUM_STICK_AXES; i++)
      {
        if(Sys.StickAxis[i].type == STICK_AXIS_ABSENT)
          continue;
        reading = analogRead(pgm_read_byte(&stickAxisPin[i]));
        Sys.StickAxis[i].centerVal = reading;
        if(reading < Sys.StickAxis[i].minVal)
          Sys.StickAxis[i].minVal = reading;
        else if(reading > Sys.StickAxis[i].maxVal)
          Sys.StickAxis[i].maxVal = reading;
      }
    }
    break;
    
    case CALIBRATE_DEADBAND:
    {
      //Add slight deadband (about 1.5%) to stabilise readings at ends
      //For a range of 0 to 5 V, min max are 0.07 V and 4.92 V
      int16_t deadBand; 
      for(uint8_t i = 0; i < NUM_STICK_AXES; i++)
      {
        deadBand = (Sys.StickAxis[i].maxVal - Sys.StickAxis[i].minVal) / 64;
        Sys.StickAxis[i].maxVal -= deadBand;
        Sys.StickAxis[i].minVal += deadBand;
      }
    }
    break;
  }
}

//==================================================================================================

void calibrateKnobs(uint8_t stage)
{
  switch(stage)
  {
    case CALIBRATE_INIT:
    {
      //set min to highest and max to lowest
      for(uint8_t i = 0; i < NUM_KNOBS; i++)
      {
        Sys.Knob[i].minVal = 1023;
        Sys.Knob[i].maxVal = 0;
      }
    }
    break;
    
    case CALIBRATE_MOVE:
    {
      //get min, max, center
      int16_t reading;
      for(uint8_t i = 0; i < NUM_KNOBS; i++)
      {
        if(Sys.Knob[i].type == KNOB_ABSENT)
          continue;
        reading = analogRead(pgm_read_byte(&knobPin[i]));
        Sys.Knob[i].centerVal = reading;
        if(reading < Sys.Knob[i].minVal)
          Sys.Knob[i].minVal = reading;
        else if(reading > Sys.Knob[i].maxVal)
          Sys.Knob[i].maxVal = reading;
      }
    }
    break;
    
    case CALIBRATE_DEADBAND:
    {
      //Add slight deadband (about 1.5%) to stabilise readings at ends
      //For a range of 0 to 5 V, min max are 0.07 V and 4.92 V
      int16_t deadBand; 
      for(uint8_t i = 0; i < NUM_KNOBS; i++)
      {
        deadBand = (Sys.Knob[i].maxVal - Sys.Knob[i].minVal) / 64;
        Sys.Knob[i].maxVal -= deadBand;
        Sys.Knob[i].minVal += deadBand;
      }
    }
    break;
  }
}
