buk7456/FreeTX/source code/transmitter/stx/stx.ino

/***************************************************************************************************
  Firmware for the RC transmitter.
  Target MCU: ATmega328P
  Compiles on Arduino 1.8.x or later
  Use compiler optimization option -O2 or -O3 if possible.
  
  Authors:
  Buk7456 (original author)
  
***************************************************************************************************/
