buk7456/FreeTX/source code/receiver/receiver.ino

/***************************************************************************************************
  Firmware for the RC receiver.
  Target MCU: ATmega328P
  Compiles on Arduino 1.8.x or later
  Use compiler optimization option -O2 or -O3 if possible.

  Notes:
  - If modifying the source code, do not use large delays inside functions that are called within the main loop; 
    rather write the source code in a non-blocking fashion.
  
  Authors:
  Buk7456 (original author)

***************************************************************************************************/
