buk7456/FreeTX/source code/transmitter/mtx/mtx.ino

/***************************************************************************************************
  Firmware for the RC transmitter
  Target MCU: ATmega2560
  Compiles on Arduino 1.8.x or later.
  - Use compiler optimization option -O2 or -O3 if possible.
  - The warning "Low memory available, stability problems may occur" can be ignored as long as
    there is at least 750 bytes available for local variables.
  
  Authors:
  Buk7456 (original author)
  
***************************************************************************************************/
