buk7456/FreeTX/source code/transmitter/mtx/src/ee/External_EEPROM.cpp

/*
  This is a library to read/write to external I2C EEPROMs.
  It uses the same template system found in the Arduino 
  EEPROM library so you can use the same get() and put() functions.

  https://github.com/sparkfun/SparkFun_External_EEPROM_Arduino_Library
  Best used with the Qwiic EEPROM: https://www.sparkfun.com/products/14764

  Various external EEPROMs have various interface specs
  (overall size, page size, write times, etc). This library works with
  all types and allows the various settings to be set at runtime.

  All read and write restrictions associated with pages are taken care of.
  You can access the external memory as if it was contiguous.

  Development environment specifics:
  Arduino IDE 1.8.x

  This library is distributed in the hope that it will be useful,
  but WITHOUT ANY WARRANTY; without even the implied warranty of
  MERCHANTABILITY or FITNESS FOR A PARTICULAR PURPOSE.  See the GNU
  Lesser General Public License for more details.
*/

#include "Arduino.h"
#include "External_EEPROM.h"
#include "Wire.h"

bool ExternalEEPROM::begin(uint8_t deviceAddress, TwoWire &wirePort)
{
  settings.i2cPort = &wirePort; //Grab which port the user wants us to use
  settings.deviceAddress = deviceAddress;

  if(isConnected() == false)
  {
    return false;
  }

  return true;
}

//Erase entire EEPROM
void ExternalEEPROM::erase(uint8_t toWrite)
{
  uint8_t tempBuffer[settings.pageSize_bytes];
  for(uint32_t x = 0; x < settings.pageSize_bytes; x++)
    tempBuffer[x] = toWrite;

  for(uint32_t addr = 0; addr < length(); addr += settings.pageSize_bytes)
    write(addr, tempBuffer, settings.pageSize_bytes);
}

uint32_t ExternalEEPROM::length()
{
  return settings.memorySize_bytes;
}

//Returns true if device is detected
bool ExternalEEPROM::isConnected(uint8_t i2cAddress)
{
  if(i2cAddress == 255)
    i2cAddress = settings.deviceAddress; //We can't set the default to settings.deviceAddress so we use 255 instead

  settings.i2cPort->beginTransmission((uint8_t)i2cAddress);
  if(settings.i2cPort->endTransmission() == 0)
    return (true);
  return (false);
}

//Returns true if device is not answering (currently writing)
//Caller can pass in an I2C address. This is helpful for larger EEPROMs that have two addresses (see block bit 2).
bool ExternalEEPROM::isBusy(uint8_t i2cAddress)
{
  if(i2cAddress == 255)
    i2cAddress = settings.deviceAddress; //We can't set the default to settings.deviceAddress so we use 255 instead

  if(isConnected(i2cAddress))
    return (false);
  return (true);
}

//void ExternalEEPROM::settings(struct_memorySettings newSettings)
//{
//  settings.deviceAddress = newSettings.deviceAddress;
//}
void ExternalEEPROM::setMemorySize(uint32_t memSize)
{
  settings.memorySize_bytes = memSize;
}
uint32_t ExternalEEPROM::getMemorySize()
{
  return settings.memorySize_bytes;
}
void ExternalEEPROM::setPageSize(uint16_t pageSize)
{
  settings.pageSize_bytes = pageSize;
}
uint16_t ExternalEEPROM::getPageSize()
{
  return settings.pageSize_bytes;
}
void ExternalEEPROM::setPageWriteTime(uint8_t writeTimeMS)
{
  settings.pageWriteTime_ms = writeTimeMS;
}
uint8_t ExternalEEPROM::getPageWriteTime()
{
  return settings.pageWriteTime_ms;
}
void ExternalEEPROM::enablePollForWriteComplete()
{
  settings.pollForWriteComplete = true;
}
void ExternalEEPROM::disablePollForWriteComplete()
{
  settings.pollForWriteComplete = false;
}
uint16_t ExternalEEPROM::getI2CBufferSize()
{
  return I2C_BUFFER_LENGTH_TX;
}
//Read a byte from a given location
uint8_t ExternalEEPROM::read(uint32_t eepromLocation)
{
  uint8_t tempByte;
  read(eepromLocation, &tempByte, 1);
  return tempByte;
}

//Bulk read from EEPROM
//Handles breaking up read amt into 32 byte chunks (can be overriden with setI2CBufferSize)
//Handles a read that straddles the 512kbit barrier
void ExternalEEPROM::read(uint32_t eepromLocation, uint8_t *buff, uint16_t bufferSize)
{
  uint16_t received = 0;
  while(received < bufferSize)
  {
    //Limit the amount to write to a page size
    uint16_t amtToRead = bufferSize - received;
    if(amtToRead > I2C_BUFFER_LENGTH_RX) //Arduino I2C buffer size limit
      amtToRead = I2C_BUFFER_LENGTH_RX;

    //Check if we are dealing with large (>512kbit) EEPROMs
    uint8_t i2cAddress = settings.deviceAddress;
    if(settings.memorySize_bytes > 0xFFFF)
    {
      //Figure out if we are going to cross the barrier with this read
      if(eepromLocation + received < 0xFFFF)
      {
        if(0xFFFF - (eepromLocation + received) < amtToRead) //0xFFFF - 0xFFFA < 32
          amtToRead = 0xFFFF - (eepromLocation + received);   //Limit the read amt to go right up to edge of barrier
      }

      //Figure out if we are accessing the lower half or the upper half
      if(eepromLocation + received > 0xFFFF)
        i2cAddress |= 0b100; //Set the block bit to 1
    }

    //See if EEPROM is available or still writing a previous request
    while(settings.pollForWriteComplete && isBusy(i2cAddress) == true) //Poll device
      delayMicroseconds(100);          //This shortens the amount of time waiting between writes but hammers the I2C bus

    settings.i2cPort->beginTransmission(i2cAddress);
    if(getMemorySize() > 2048)
      settings.i2cPort->write((uint8_t)((eepromLocation + received) >> 8));   // MSB
    settings.i2cPort->write((uint8_t)((eepromLocation + received) & 0xFF)); // LSB
    settings.i2cPort->endTransmission();

    settings.i2cPort->requestFrom((uint8_t)i2cAddress, (uint8_t)amtToRead);

    for(uint16_t x = 0; x < amtToRead; x++)
      buff[received + x] = settings.i2cPort->read();

    received += amtToRead;
  }
}

//Write a byte to a given location
void ExternalEEPROM::write(uint32_t eepromLocation, uint8_t dataToWrite)
{
  if(read(eepromLocation) != dataToWrite) //Update only if data is new
    write(eepromLocation, &dataToWrite, 1);
}

//Write large bulk amounts
//Limits writes to the I2C buffer size (default is 32 bytes)
void ExternalEEPROM::write(uint32_t eepromLocation, const uint8_t *dataToWrite, uint16_t bufferSize)
{
  //Error check
  if(eepromLocation + bufferSize >= settings.memorySize_bytes)
    bufferSize = settings.memorySize_bytes - eepromLocation;

  uint16_t maxWriteSize = settings.pageSize_bytes;
  if(maxWriteSize > I2C_BUFFER_LENGTH_TX - 2)
    maxWriteSize = I2C_BUFFER_LENGTH_TX - 2; //Arduino has 32 byte limit. We loose two to the EEPROM address

  //Break the buffer into page sized chunks
  uint16_t recorded = 0;
  while(recorded < bufferSize)
  {
    //Limit the amount to write to either the page size or the Arduino limit of 30
    uint16_t amtToWrite = bufferSize - recorded;
    if(amtToWrite > maxWriteSize)
      amtToWrite = maxWriteSize;

    if(amtToWrite > 1)
    {
      //Check for crossing of a page line. Writes cannot cross a page line.
      uint16_t pageNumber1 = (eepromLocation + recorded) / settings.pageSize_bytes;
      uint16_t pageNumber2 = (eepromLocation + recorded + amtToWrite - 1) / settings.pageSize_bytes;
      if(pageNumber2 > pageNumber1)
        amtToWrite = (pageNumber2 * settings.pageSize_bytes) - (eepromLocation + recorded); //Limit the read amt to go right up to edge of page barrier
    }

    uint8_t i2cAddress = settings.deviceAddress;
    //Check if we are dealing with large (>512kbit) EEPROMs
    if(settings.memorySize_bytes > 0xFFFF)
    {
      //Figure out if we are accessing the lower half or the upper half
      if(eepromLocation + recorded > 0xFFFF)
        i2cAddress |= 0b100; //Set the block bit to 1
    }

    //See if EEPROM is available or still writing a previous request
    while(settings.pollForWriteComplete && isBusy(i2cAddress) == true) //Poll device
      delayMicroseconds(100);          //This shortens the amount of time waiting between writes but hammers the I2C bus

    settings.i2cPort->beginTransmission(i2cAddress);
    if(getMemorySize() > 2048)
      settings.i2cPort->write((uint8_t)((eepromLocation + recorded) >> 8));   // MSB
    settings.i2cPort->write((uint8_t)((eepromLocation + recorded) & 0xFF)); // LSB
    for(uint8_t x = 0; x < amtToWrite; x++)
      settings.i2cPort->write(dataToWrite[recorded + x]);
    settings.i2cPort->endTransmission(); //Send stop condition

    recorded += amtToWrite;

    if(settings.pollForWriteComplete == false)
      delay(settings.pageWriteTime_ms); //Delay the amount of time to record a page
  }
}
