buk7456/FreeTX/source code/transmitter/mtx/src/ee/External_EEPROM.h

/*
  This is a library to read/write to external I2C EEPROMs.
  It uses the same template system found in the Arduino 
  EEPROM library so you can use the same get() and put() functions.

  https://github.com/sparkfun/SparkFun_External_EEPROM_Arduino_Library
  Best used with the Qwiic EEPROM: https://www.sparkfun.com/products/14764

  Various external EEPROMs have various interface specs
  (overall size, page size, write times, etc). This library works with
  all types and allows the various settings to be set at runtime.

  All read and write restrictions associated with pages are taken care of.
  You can access the external memory as if it was contiguous.

  Development environment specifics:
  Arduino IDE 1.8.x

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
*/

#ifndef _EXTERNAL_EEPROM_SPARKFUN_H
#define _EXTERNAL_EEPROM_SPARKFUN_H

#include "Arduino.h"
#include "Wire.h"

#if defined(ARDUINO_ARCH_APOLLO3)

#define I2C_BUFFER_LENGTH_RX 256 //Hardcoding until issue is resolved: https://github.com/sparkfun/Arduino_Apollo3/issues/351
#define I2C_BUFFER_LENGTH_TX 256

#elif defined(__AVR_ATmega328P__) || defined(__AVR_ATmega168__)

#define I2C_BUFFER_LENGTH_RX BUFFER_LENGTH //I2C_BUFFER_LENGTH is defined in Wire.H
#define I2C_BUFFER_LENGTH_TX BUFFER_LENGTH

#elif defined(__SAMD21G18A__)

#define I2C_BUFFER_LENGTH_RX SERIAL_BUFFER_SIZE //SAMD21 uses RingBuffer.h
#define I2C_BUFFER_LENGTH_TX SERIAL_BUFFER_SIZE

#elif (defined(__MK20DX128__) || defined(__MK20DX256__) || defined(__MKL26Z64__) || defined(__MK64FX512__) || defined(__MK66FX1M0__) || defined(__IMXRT1062__)) // 3.0/3.1-3.2/LC/3.5/3.6/4.0

#define I2C_BUFFER_LENGTH_RX BUFFER_LENGTH //Teensy
#define I2C_BUFFER_LENGTH_TX BUFFER_LENGTH

#elif defined(ESP32)

#define I2C_BUFFER_LENGTH_RX I2C_BUFFER_LENGTH
#define I2C_BUFFER_LENGTH_TX I2C_BUFFER_LENGTH

#elif defined(STM32)

#define I2C_BUFFER_LENGTH_RX BUFFER_LENGTH //BUFFER_LENGTH is defined in Wire.h for STM32
#define I2C_BUFFER_LENGTH_TX BUFFER_LENGTH

#elif defined(NRF52_SERIES)

#define I2C_BUFFER_LENGTH_RX SERIAL_BUFFER_SIZE //Adafruit Bluefruit nRF52 Boards uses RingBuffer.h
#define I2C_BUFFER_LENGTH_TX SERIAL_BUFFER_SIZE

#else

// #pragma GCC warning "This platform doesn't have a wire buffer size defined. Defaulting to 32 bytes. Please contribute to this library!"

//Default to safe 32 bytes
#define I2C_BUFFER_LENGTH_RX 32
#define I2C_BUFFER_LENGTH_TX 32

#endif

struct struct_memorySettings
{
  TwoWire *i2cPort;
  uint8_t deviceAddress;
  uint32_t memorySize_bytes;
  uint16_t pageSize_bytes;
  uint8_t pageWriteTime_ms;
  bool pollForWriteComplete;
  // uint16_t i2cBufferSize;
};

class ExternalEEPROM
{
public:
  uint8_t read(uint32_t eepromLocation);
  void read(uint32_t eepromLocation, uint8_t *buff, uint16_t bufferSize);
  void write(uint32_t eepromLocation, uint8_t dataToWrite);
  void write(uint32_t eepromLocation, const uint8_t *dataToWrite, uint16_t blockSize);

  bool begin(uint8_t deviceAddress = 0b1010000, TwoWire &wirePort = Wire); //By default use the Wire port
  bool isConnected(uint8_t i2cAddress = 255);
  bool isBusy(uint8_t i2cAddress = 255);
  void erase(uint8_t toWrite = 0x00); //Erase the entire memory. Optional: write a given byte to each spot.

  //void settings(struct_memorySettings newSettings); //Set all the settings using the settings struct
  void setMemorySize(uint32_t memSize); //Set the size of memory in bytes
  uint32_t getMemorySize();             //Return size of EEPROM
  uint32_t length();                    //Return size of EEPROM
  void setPageSize(uint16_t pageSize);  //Set the size of the page we can write at a time
  uint16_t getPageSize();
  void setPageWriteTime(uint8_t writeTimeMS); //Set the number of ms required per page write
  uint8_t getPageWriteTime();
  void enablePollForWriteComplete(); //Most EEPROMs all I2C polling of when a write has completed
  void disablePollForWriteComplete();
  uint16_t getI2CBufferSize(); //Return the size of the TX buffer

  //Functionality to 'get' and 'put' objects to and from EEPROM.
  template <typename T>
  T &get(uint32_t idx, T &t)
  {
    uint8_t *ptr = (uint8_t *)&t;
    read(idx, ptr, sizeof(T)); //Address, data, sizeOfData
    return t;
  }

  template <typename T>
  const T &put(uint32_t idx, const T &t) //Address, data
  {
    const uint8_t *ptr = (const uint8_t *)&t;
    write(idx, ptr, sizeof(T)); //Address, data, sizeOfData
    return t;
  }

private:
  //Variables
  struct_memorySettings settings = {
      .i2cPort = &Wire,
      .deviceAddress = 0b1010000, //0b1010 + (A2 A1 A0) or 0b1010 + (B0 A1 A0) for larger (>512kbit) EEPROMs
      .memorySize_bytes = 512000 / 8,
      .pageSize_bytes = 64,
      .pageWriteTime_ms = 5,
      .pollForWriteComplete = true,
  };
};

#endif //_EXTERNAL_EEPROM_SPARKFUN_H
