buk7456/FreeTX/tests/rc_data_encode_decode/rc_data_encode_decode.ino

#include "Arduino.h"

#define NUM_RC_CHANNELS 20

#define FIXED_PAYLOAD_SIZE ((((NUM_RC_CHANNELS * 10) + 7) / 8) + 1)

#if FIXED_PAYLOAD_SIZE < 10
  #undef  FIXED_PAYLOAD_SIZE
  #define FIXED_PAYLOAD_SIZE  10
#endif

void testEncDec()
{
  int16_t channelOut[NUM_RC_CHANNELS];
  //fill with random data
  randomSeed(analogRead(A0));
  for(uint8_t i = 0; i < NUM_RC_CHANNELS; i++)
  {
    channelOut[i] = random(-500, 500);
  }
  
  //--------- encode -----------
  uint32_t encTimeQQ = micros();
  uint8_t dataBuff[FIXED_PAYLOAD_SIZE];
  memset(dataBuff, 0, sizeof(dataBuff));
  for(uint8_t chIdx = 0; chIdx < NUM_RC_CHANNELS; chIdx++)
  {
    uint16_t val = (channelOut[chIdx] + 500) & 0xFFFF; 
    //encode into 10bit resolution bitstream
    uint8_t aIdx = chIdx + (chIdx / 4);
    uint8_t bIdx = aIdx + 1;
    uint8_t aShift = ((chIdx % 4) + 1) * 2;
    uint8_t bShift = 8 - aShift;
    dataBuff[aIdx] |= ((val >> aShift) & 0xFF);
    dataBuff[bIdx] |= ((val << bShift) & 0xFF);
  }
  encTimeQQ = micros() - encTimeQQ;

  //-------- Decode -----------
  uint32_t decTimeQQ = micros();
  uint16_t chData[NUM_RC_CHANNELS];
  for(uint8_t chIdx = 0; chIdx < NUM_RC_CHANNELS; chIdx++)
  {
    uint8_t aIdx = chIdx + (chIdx / 4);
    uint8_t bIdx = aIdx + 1;
    uint8_t aShift = ((chIdx % 4) + 1) * 2;
    uint8_t bShift = 8 - aShift;
    uint16_t aMask = ((uint16_t)0x0400) - ((uint16_t)1 << aShift);
    uint8_t  bMask = ((uint16_t)1 << (8-bShift)) - 1;
    
    chData[chIdx] = (((uint16_t)dataBuff[aIdx] << aShift) & aMask) | (((uint16_t)dataBuff[bIdx] >> bShift) & bMask);
  }
  decTimeQQ = micros() - decTimeQQ;
  
  //-------- Print the input output ---------
  Serial.print("\r\nEncode time: ");
  Serial.print(encTimeQQ);
  Serial.print("us\r\n");
  Serial.print("Decode time: ");
  Serial.print(decTimeQQ);
  Serial.print("us\r\n");

  Serial.print("Input, Output\r\n");
  for(uint8_t chIdx = 0; chIdx < NUM_RC_CHANNELS; chIdx++)
  {
    Serial.print("Ch");
    Serial.print(chIdx + 1);
    Serial.print(": ");
    Serial.print(channelOut[chIdx]);
    Serial.print(", ");
    int16_t val = chData[chIdx];
    val -= 500;
    Serial.print(val);
    Serial.println();
  }
}

void setup()
{
  Serial.begin(9600);
  delay(1000);
}

void loop()
{
  Serial.print("\r\n======== 10 bit encode decode test ===========\r\n");
  for(uint8_t cnt = 0; cnt < 10; cnt++)
  {
    Serial.print("\r\n----- Run ");
    Serial.print(cnt + 1);
    Serial.print(" of 10 ------\r\n");
    
    testEncDec();
    delay(2000);
  }
  
  Serial.print("\r\nTest completed\r\n");
  
  while(1)
  {
  }
}
