buk7456/FreeTX/source code/transmitter/mtx/src/ui/ui_128x64/ui_mixer.cpp

#include "ui_128x64.h"

#if defined (UI_128X64)

void ui_handler_mixer()
{
  switch(theScreen)
  {
    case SCREEN_MIXER:
      {
        drawHeader(mainMenu[MAIN_MENU_MIXER]);
        
        mixer_params_t *mxr = &Model.Mixer[thisMixIdx];
        
        //For safety and to prevent unintended effects, we do not directly edit the mixer output variable 
        //but instead use some kind of delayed action, where we edit a temporary variable 
        //and later assign it to the output in the right conditions.
        static uint8_t tempMixerOutput;
        static bool tempInitialised = false;
        if(!tempInitialised)
        {
          tempMixerOutput = mxr->output;
          tempInitialised = true;
        }
        
        display.setCursor(8, 9);
        display.print(F("Mix"));
        display.print(thisMixIdx + 1);
        if(!isEmptyStr(mxr->name, sizeof(mxr->name)))
        {
          display.setCursor(display.getCursorX() + 6, 9);
          display.print(mxr->name);
        }
        display.drawHLine(8, 17, display.getCursorX() - 9, BLACK);

        //--- Dynamic list ---
        
        enum {
          ITEM_MIX_OUTPUT,
          ITEM_MIX_SWITCH,
          ITEM_MIX_OPERATION,
          ITEM_MIX_INPUT,
          ITEM_MIX_WEIGHT,
          ITEM_MIX_OFFSET,
          ITEM_MIX_CURVE_TYPE,
          ITEM_MIX_CURVE_VAL,
          ITEM_MIX_TRIM_ENABLED,
          ITEM_MIX_FLIGHT_MODE,
          ITEM_MIX_DELAY_UP,
          ITEM_MIX_DELAY_DOWN,
          ITEM_MIX_SLOW_UP,
          ITEM_MIX_SLOW_DOWN,
          
          ITEM_COUNT
        };
        
        uint8_t listItemIDs[ITEM_COUNT]; //stores the added item IDs
        uint8_t listItemCount = 0;
        
        //add item Ids to the list of Ids
        for(uint8_t i = 0; i < sizeof(listItemIDs); i++)
        {
          if(mxr->operation == MIX_HOLD)
          {
            if(i != ITEM_MIX_OUTPUT && i != ITEM_MIX_SWITCH && i!= ITEM_MIX_OPERATION)
              continue;
          }
          if(i == ITEM_MIX_FLIGHT_MODE)
          {
            if(Model.type == MODEL_TYPE_AIRPLANE || Model.type == MODEL_TYPE_MULTICOPTER)
              listItemIDs[listItemCount++] = i;
            continue;
          }
          listItemIDs[listItemCount++] = i;
        }
        
        //initialise the view
        static uint8_t topItem;
        static uint8_t lastFocusedItem;
        static bool viewInitialised = false;
        if(!viewInitialised)
        {
          focusedItem = 1;
          lastFocusedItem = 1;
          topItem = 1;
          viewInitialised = true;
        }

        bool hasCrossHairs = true;
        
        //handle navigation
        focusedItem = lastFocusedItem;
        uint8_t numFocusable = listItemCount + 2; //+1 for title focus, +1 for context menu focus
        changeFocusOnUpDown(numFocusable); 
        toggleEditModeOnSelectClicked();
        if(focusedItem == 1 || focusedItem == numFocusable) //title focus or context menu focus
          topItem = 1;
        else if(focusedItem > 1)
        {
          if(focusedItem - 1 < topItem)
            topItem = focusedItem - 1;
          while(focusedItem - 1 >= topItem + 5)
            topItem++;
        }
        lastFocusedItem = focusedItem;
        
        //fill list and edit items
        for(uint8_t line = 0; line < 5 && line < listItemCount; line++)
        {
          uint8_t ypos = 20 + line*9;
          if(focusedItem - 1 == topItem + line)
            drawCursor(48, ypos);
          
          if((topItem - 1 + line) >= listItemCount)
            break;
    
          uint8_t itemID = listItemIDs[topItem - 1 + line];
          bool isFocused = (focusedItem > 1 && focusedItem != numFocusable && itemID == listItemIDs[focusedItem - 2]);
          bool edit = (isFocused && isEditMode);
          
          display.setCursor(0, ypos);
          switch(itemID)
          {
            case ITEM_MIX_OUTPUT:
              {
                display.print(F("Output:"));
                display.setCursor(56, ypos);
                getSrcName(textBuff, tempMixerOutput, sizeof(textBuff));
                display.print(textBuff);
                if(tempMixerOutput >= SRC_CH1 && tempMixerOutput < SRC_CH1 + NUM_RC_CHANNELS)
                {
                  uint8_t chIdx = tempMixerOutput - SRC_CH1;
                  display.setCursor(display.getCursorX() + 6, ypos);
                  display.print(Model.Channel[chIdx].name);
                }
                if(edit && (buttonCode == KEY_UP || buttonCode == KEY_DOWN))
                {
                  do {
                  tempMixerOutput = incDecSource(tempMixerOutput, INCDEC_FLAG_MIX_SRC);
                  } while(tempMixerOutput > SRC_NONE && tempMixerOutput < SRC_CH1); //skip over
                }                
              }
              break;

            case ITEM_MIX_SWITCH:
              {
                display.print(F("Switch:"));
                display.setCursor(56, ypos);
                getControlSwitchName(textBuff, mxr->swtch, sizeof(textBuff));
                display.print(textBuff);
                if(edit)
                  mxr->swtch = incDecControlSwitch(mxr->swtch);
              }
              break;
            
            case ITEM_MIX_OPERATION:
              {
                display.print(F("Opertn:"));
                display.setCursor(56, ypos);
                display.print(findStringInIdStr(enum_MixerOperation, mxr->operation));
                if(edit)
                  mxr->operation = incDec(mxr->operation, 0, MIX_OPERATOR_COUNT - 1, INCDEC_WRAP, INCDEC_SLOW);
              }
              break;
              
            case ITEM_MIX_INPUT:
              {
                display.print(F("Input:"));
                display.setCursor(56, ypos);
                getSrcName(textBuff, mxr->input, sizeof(textBuff));
                display.print(textBuff);
                if(edit)
                {
                  //auto detect moved source
                  uint8_t movedSrc = procMovedSource(getMovedSource());
                  if(movedSrc != SRC_NONE)
                    mxr->input = movedSrc;
                  //inc dec
                  mxr->input = incDecSource(mxr->input, INCDEC_FLAG_MIX_SRC | INCDEC_FLAG_COUNTER_AS_SRC);
                  //hide cross hairs on the graph to minimise distraction when editing the input
                  if(buttonCode == KEY_UP || buttonCode == KEY_DOWN)
                    hasCrossHairs = false;
                }
              }
              break;
              
            case ITEM_MIX_WEIGHT:
              {
                display.print(F("Weight:"));
                display.setCursor(56, ypos);
                display.print(mxr->weight);
                if(edit)
                  mxr->weight = incDec(mxr->weight, -100, 100, INCDEC_NOWRAP, INCDEC_NORMAL);
              }
              break;
              
            case ITEM_MIX_OFFSET:
              {
                display.print(F("Offset:"));
                display.setCursor(56, ypos);
                display.print(mxr->offset);
                if(edit)
                  mxr->offset = incDec(mxr->offset, -100, 100, INCDEC_NOWRAP, INCDEC_NORMAL);
              }
              break;
              
            case ITEM_MIX_CURVE_TYPE:
              {
                display.print(F("Curve:"));
                display.setCursor(56, ypos);
                display.print(findStringInIdStr(enum_MixerCurveType, mxr->curveType));
                if(edit)
                {
                  uint8_t prevCurveType = mxr->curveType;
                  mxr->curveType = incDec(mxr->curveType, 0, MIX_CURVE_TYPE_COUNT - 1, INCDEC_WRAP, INCDEC_SLOW);
                  if(mxr->curveType != prevCurveType) 
                    mxr->curveVal = 0; //reset value if changed
                }
              }
              break;
              
            case ITEM_MIX_CURVE_VAL:
              {
                display.print(F("Crv val:"));
                display.setCursor(56, ypos);
                if(mxr->curveType == MIX_CURVE_TYPE_DIFF || mxr->curveType == MIX_CURVE_TYPE_EXPO)
                  display.print(mxr->curveVal);
                else if(mxr->curveType == MIX_CURVE_TYPE_FUNCTION)
                  display.print(findStringInIdStr(enum_MixerCurveType_Func, mxr->curveVal));
                else if(mxr->curveType == MIX_CURVE_TYPE_CUSTOM)
                {
                  if(isEmptyStr(Model.CustomCurve[mxr->curveVal].name, sizeof(Model.CustomCurve[0].name)))
                  {
                    display.print(F("Crv"));
                    display.print(mxr->curveVal + 1);
                  }
                  else
                    display.print(Model.CustomCurve[mxr->curveVal].name);
                }
                if(edit)
                {
                  if(mxr->curveType == MIX_CURVE_TYPE_DIFF || mxr->curveType == MIX_CURVE_TYPE_EXPO)
                    mxr->curveVal = incDec(mxr->curveVal, -100, 100, INCDEC_NOWRAP, INCDEC_NORMAL);
                  else if(mxr->curveType == MIX_CURVE_TYPE_FUNCTION)
                    mxr->curveVal = incDec(mxr->curveVal, 0, MIX_CURVE_FUNC_COUNT - 1, INCDEC_WRAP, INCDEC_SLOW);
                  else if(mxr->curveType == MIX_CURVE_TYPE_CUSTOM)
                    mxr->curveVal = incDec(mxr->curveVal, 0, NUM_CUSTOM_CURVES - 1, INCDEC_WRAP, INCDEC_SLOW);
                }
              }
              break;
              
            case ITEM_MIX_TRIM_ENABLED:
              {
                display.print(F("Trim:"));
                display.setCursor(56, ypos);
                uint8_t input = mxr->input;
                if(input == SRC_RUD) input = Model.rudSrcRaw;
                if(input == SRC_THR) input = Model.thrSrcRaw;
                if(input == SRC_AIL) input = Model.ailSrcRaw;
                if(input == SRC_ELE) input = Model.eleSrcRaw;
                if(input == SRC_X1_AXIS || input == SRC_Y1_AXIS || input == SRC_X2_AXIS || input == SRC_Y2_AXIS)
                {
                  drawCheckbox(56, ypos, mxr->trimEnabled);
                  if(edit)
                    mxr->trimEnabled = incDec(mxr->trimEnabled, 0, 1, INCDEC_WRAP, INCDEC_PRESSED);
                }
                else
                  display.print(F("N/A"));
              }
              break;
              
            case ITEM_MIX_FLIGHT_MODE:
              {
                display.print(F("F-mode:"));
                display.setCursor(56, ypos);
                if(mxr->flightMode == 0xff)
                  display.print(F("All"));
                else
                {
                  bool delimit = false;
                  for(uint8_t i = 0; i < NUM_FLIGHT_MODES; i++)
                  {
                    if((mxr->flightMode >> i) & 0x01)
                    {
                      if(delimit)
                        display.print(F(","));
                      display.print(i+1);
                      delimit = true;
                    }
                  }
                }
                if(edit)
                  changeToScreen(DIALOG_MIX_FLIGHT_MODE);
              }
              break;
              
            case ITEM_MIX_DELAY_UP:
              {
                display.print(F("Dly up:"));
                display.setCursor(56, ypos);
                printSeconds(mxr->delayUp);
                if(edit)
                  mxr->delayUp = incDec(mxr->delayUp, 0, 600, INCDEC_NOWRAP, INCDEC_SLOW, INCDEC_NORMAL);
              }
              break;
              
            case ITEM_MIX_DELAY_DOWN:
              {
                display.print(F("Dly dn:"));
                display.setCursor(56, ypos);
                printSeconds(mxr->delayDown);
                if(edit)
                  mxr->delayDown = incDec(mxr->delayDown, 0, 600, INCDEC_NOWRAP, INCDEC_SLOW, INCDEC_NORMAL);
              }
              break;
              
            case ITEM_MIX_SLOW_UP:
              {
                display.print(F("Slow up:"));
                display.setCursor(56, ypos);
                printSeconds(mxr->slowUp);
                if(edit)
                  mxr->slowUp = incDec(mxr->slowUp, 0, 600, INCDEC_NOWRAP, INCDEC_SLOW, INCDEC_NORMAL);
              }
              break;
              
            case ITEM_MIX_SLOW_DOWN:
              {
                display.print(F("Slow dn:"));
                display.setCursor(56, ypos);
                printSeconds(mxr->slowDown);
                if(edit)
                  mxr->slowDown = incDec(mxr->slowDown, 0, 600, INCDEC_NOWRAP, INCDEC_SLOW, INCDEC_NORMAL);
              }
              break;
          }
        }
        
        //Draw scroll bar
        drawScrollBar(127, 19, listItemCount, topItem, 5, 5 * 9);
        
        //Draw mixer curve preview
        focusedMixIdx = thisMixIdx;
        if(Sys.showCurvePreviewInMixer && mxr->operation != MIX_HOLD)
          drawMixerCurvePreview(mxr, hasCrossHairs);
        
        //Show context menu icon
        display.fillRect(120, 0, 8, 7, WHITE);
        display.drawBitmap(120, 0, focusedItem == numFocusable ? icon_context_menu_focused : icon_context_menu, 8, 7, BLACK);
        
        //Assign from temp
        if(!isEditMode || (buttonCode == 0 && millis() - buttonReleaseTime > 1000))
        {
          mxr->output = tempMixerOutput;
          tempInitialised = false;
        }
        
        //change to next mix
        if(focusedItem == 1)
        {
          drawCursor(0, 9);
          if(isEditMode)
          {
            //assign from temp
            mxr->output = tempMixerOutput;
            tempInitialised = false;
            //change to another mix
            uint8_t prevMixIdx = thisMixIdx;
            thisMixIdx = incDec(thisMixIdx, 0, NUM_MIX_SLOTS - 1, INCDEC_WRAP, INCDEC_SLOW);
            if(thisMixIdx != prevMixIdx)
              graphYCoordinatesInvalid = true;
          }
        }
        
        //Open context menu
        if(focusedItem == numFocusable && clickedButton == KEY_SELECT)
        {
          changeToScreen(CONTEXT_MENU_MIXER);
          viewInitialised = false;
          //assign from temp
          mxr->output = tempMixerOutput;
          tempInitialised = false;
        }

        //Exit
        if(heldButton == KEY_SELECT)
        {
          viewInitialised = false;
          changeToScreen(SCREEN_MAIN_MENU);
          //assign from temp
          mxr->output = tempMixerOutput; 
          tempInitialised = false;
        } 
      }
      break;
      
    case DIALOG_MIX_FLIGHT_MODE:
      {
        //--- scrollable list

        //handle navigation
        changeFocusOnUpDown(NUM_FLIGHT_MODES);
        static uint8_t topItem = 1;
        if(focusedItem < topItem)
          topItem = focusedItem;
        while(focusedItem >= topItem + 4)
          topItem++;
        
        //Calculate y coordinate for item 0. Items are center aligned
        uint8_t numVisible = NUM_FLIGHT_MODES <= 4 ? NUM_FLIGHT_MODES : 4;
        uint8_t y0 = ((display.height() - (numVisible * 9)) / 2) + 1;  //9 is line height
        
        //draw bounding box
        drawBoundingBox(11, y0 - 3, 105, numVisible * 9 + 4, BLACK);
        
        //fill list
        for(uint8_t line = 0; line < numVisible; line++)
        {
          uint8_t ypos = y0 + line * 9;
          uint8_t item = topItem + line;
          if(focusedItem == item)
            drawCursor(17, ypos);
          uint8_t idx = item - 1;
          drawCheckbox(25, ypos, Model.Mixer[thisMixIdx].flightMode & (1 << idx));
          display.setCursor(35, ypos);
          getControlSwitchName(textBuff, CTRL_SW_FMD_FIRST + idx, sizeof(textBuff));
          display.print(textBuff);
          display.print(F(" "));
          display.print(Model.FlightMode[idx].name);
        }
        
        //scroll bar
        uint8_t  y = Sys.useRoundRect ? y0 : y0 - 1;
        uint16_t h = Sys.useRoundRect ? numVisible * 9 - 2 : numVisible * 9;
        drawScrollBar(112, y, NUM_FLIGHT_MODES, topItem, numVisible, h);
        
        //--- edit items
        toggleEditModeOnSelectClicked();
        if(isEditMode && (pressedButton == KEY_UP || pressedButton == KEY_DOWN))
        {
          uint8_t idx = focusedItem - 1;
          Model.Mixer[thisMixIdx].flightMode ^= 1 << idx; //toggle bit
        }
        
        //--- exit 
        if(heldButton == KEY_SELECT)
        {
          if((Model.Mixer[thisMixIdx].flightMode & (uint8_t)((1 << NUM_FLIGHT_MODES) - 1)) == 0) //nothing selected
          {
            killButtonEvents();
            makeToast(PSTR("Select at least one"), 2000, 0);
          }
          else 
            changeToScreen(SCREEN_MIXER);
        }
      }
      break;
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
