buk7456/FreeTX/source code/transmitter/mtx/src/ui/ui_128x64/ui_system_settings.cpp

#include "ui_128x64.h"

#if defined (UI_128X64)

void ui_handler_system_settings()
{
  switch(theScreen)
  {
    case SCREEN_SYSTEM_MENU:
      {
        drawHeader_Menu(mainMenu[MAIN_MENU_SYSTEM]);
        
        static uint8_t topItem = 1, highlightedItem = 1;

        menuInitialise();
        menuAddItem(systemMenu[SYSTEM_MENU_RF], SYSTEM_MENU_RF, NULL);
        menuAddItem(systemMenu[SYSTEM_MENU_SOUND], SYSTEM_MENU_SOUND, NULL);
        menuAddItem(systemMenu[SYSTEM_MENU_BACKLIGHT], SYSTEM_MENU_BACKLIGHT, NULL);
        menuAddItem(systemMenu[SYSTEM_MENU_APPEARANCE], SYSTEM_MENU_APPEARANCE, NULL);
        menuAddItem(systemMenu[SYSTEM_MENU_MISCELLANEOUS], SYSTEM_MENU_MISCELLANEOUS, NULL);
        menuAddItem(systemMenu[SYSTEM_MENU_ADVANCED], SYSTEM_MENU_ADVANCED, NULL);
        menuAddItem(systemMenu[SYSTEM_MENU_ABOUT], SYSTEM_MENU_ABOUT, NULL);
        menuDraw(&topItem, &highlightedItem);

        if(menuSelectedItemID == SYSTEM_MENU_RF) changeToScreen(SCREEN_RF);
        else if(menuSelectedItemID == SYSTEM_MENU_SOUND) changeToScreen(SCREEN_SOUND);
        else if(menuSelectedItemID == SYSTEM_MENU_BACKLIGHT) changeToScreen(SCREEN_BACKLIGHT);
        else if(menuSelectedItemID == SYSTEM_MENU_APPEARANCE) changeToScreen(SCREEN_APPEARANCE);
        else if(menuSelectedItemID == SYSTEM_MENU_MISCELLANEOUS) changeToScreen(SCREEN_MISCELLANEOUS);
        else if(menuSelectedItemID == SYSTEM_MENU_ABOUT) changeToScreen(SCREEN_ABOUT);
        else if(menuSelectedItemID == SYSTEM_MENU_ADVANCED)
        {
          if(!isEmptyStr(Sys.password, sizeof(Sys.password))) 
            changeToScreen(SCREEN_UNLOCK_ADVANCED_MENU); //prompt to enter password first
          else //no password specified, don't prompt
            changeToScreen(SCREEN_ADVANCED_MENU);
        }

        //exit
        if(heldButton == KEY_SELECT)
        {
          if(!Sys.rememberMenuPosition)
          {
            topItem = 1;
            highlightedItem = 1;
          }
          changeToScreen(SCREEN_MAIN_MENU);
        }
      }
      break;
      
    case SCREEN_RF:
      {
        drawHeader(systemMenu[SYSTEM_MENU_RF]);
        
        display.setCursor(0, 9);
        display.print(F("RF output:"));
        drawCheckbox(72, 9, Sys.rfEnabled);
      
        display.setCursor(0, 18);
        display.print(F("RF power:"));
        display.setCursor(72, 18);
        display.print(findStringInIdStr(enum_RFpower, Sys.rfPower));
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
