buk7456/FreeTX/source code/transmitter/mtx/src/ui/ui_128x64/ui_home.cpp

#include "ui_128x64.h"

#if defined (UI_128X64)

void ui_handler_home()
{
  switch(theScreen)
  {
    case SCREEN_HOME:
      {
        if(isRequestingSettingsRestore)
        {
          if(sdHasCard() && sdSystemSettingsExists())
          {
            changeToScreen(CONFIRMATION_RESTORE_SYSTEM_SETTINGS);
            break;
          }
          else
            isRequestingSettingsRestore = false;
        }

        if(isRequestingStickCalibration)
        {
          changeToScreen(SCREEN_STICKS);
          break; 
        }
        
        if(isRequestingKnobCalibration)
        {
          changeToScreen(SCREEN_KNOBS);
          break; 
        }

        if(isRequestingSwitchesSetup)
        {
          changeToScreen(SCREEN_SWITCHES);
          break;
        }
        
        if(!batteryGaugeCalibrated)
        {
          changeToScreen(SCREEN_BATTERY);
          break;
        }
        
        if((!Sys.lockStartup && !Sys.lockOnInactivity) || isEmptyStr(Sys.password, sizeof(Sys.password)))
          mainMenuLocked = false;
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
